Schepie/7segment/Images/7segment_exploded.png

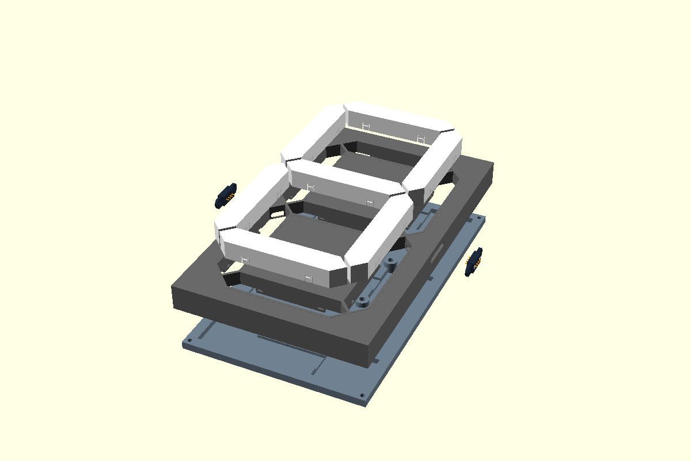
Images/7segment_exploded.png
