Schepie/7segment/Images/20261002_122156.jpg

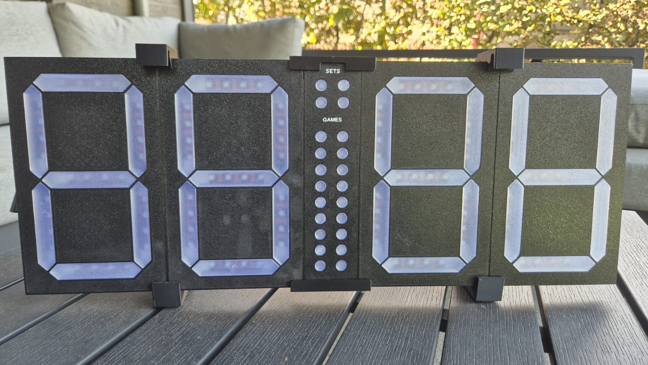
Images/20261002_122156.jpg
