Schepie/7segment/Images/20261002_122202.jpg

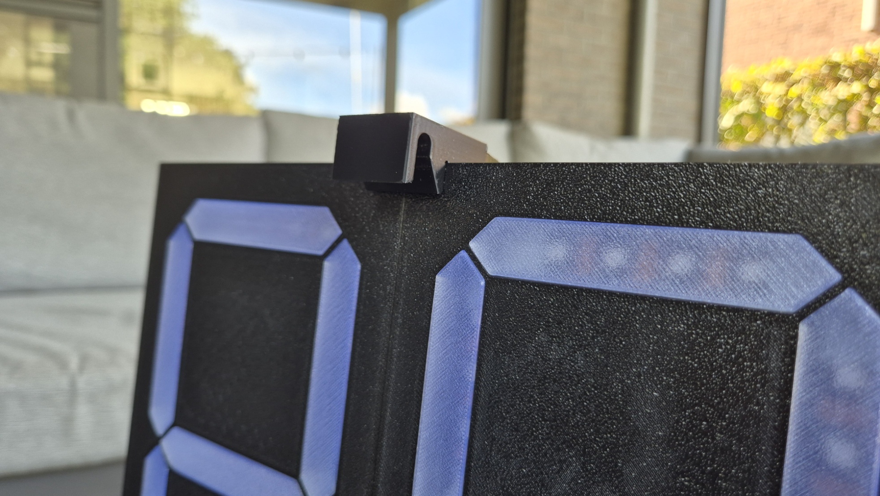
Images/20261002_122202.jpg
