Schepie/7segment/Images/20261002_122213.jpg

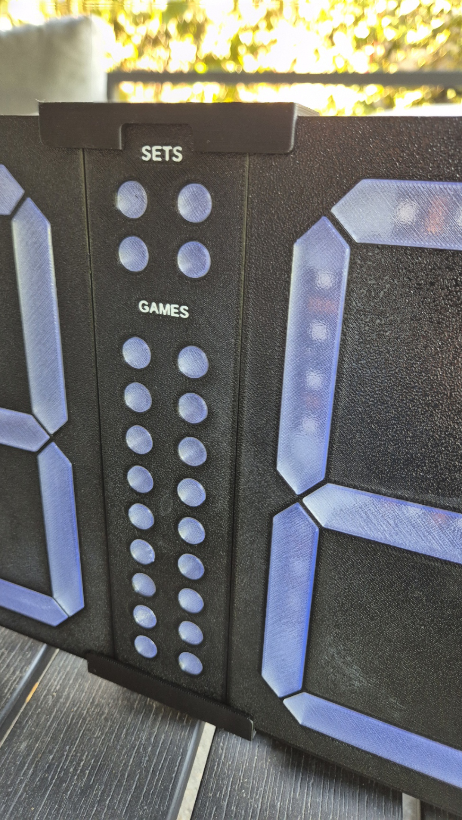
Images/20261002_122213.jpg
