Schepie/7segment/Images/20261002_122249.jpg

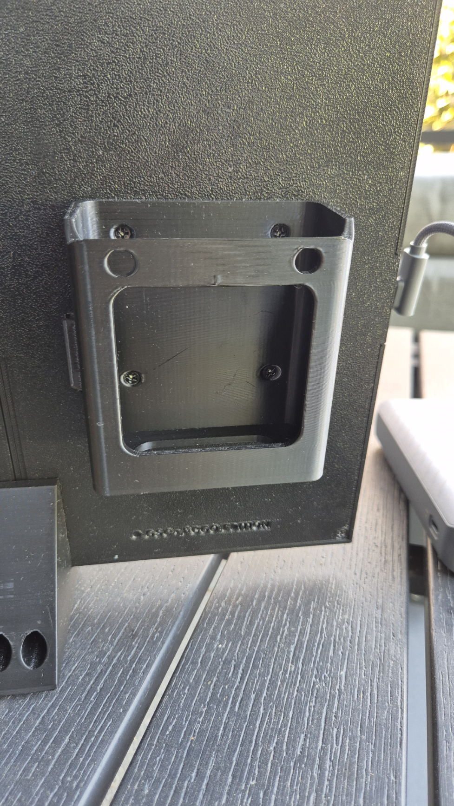
Images/20261002_122249.jpg
