Schepie/7segment/Images/20261002_122254.jpg

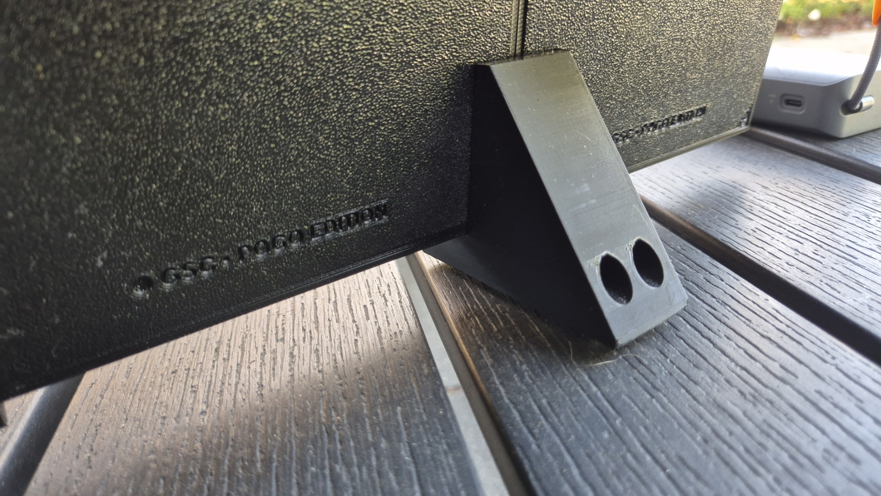
Images/20261002_122254.jpg
