Schepie/7segment/Images/20261002_122310.jpg

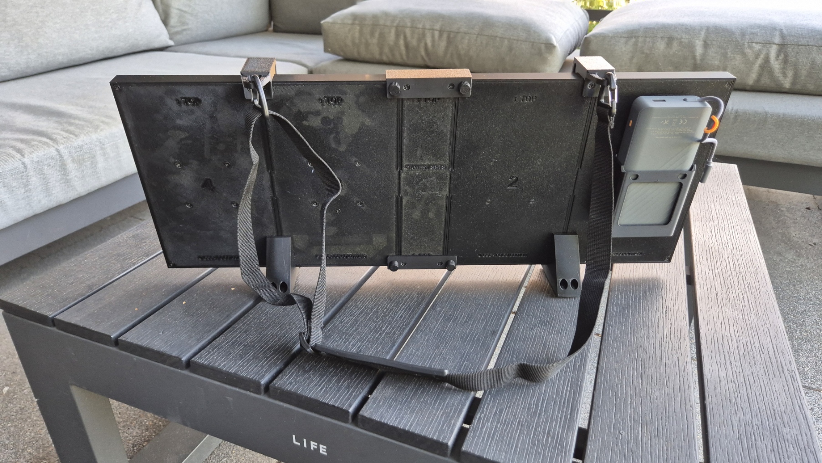
Images/20261002_122310.jpg
