Schepie/7segment/Images/20261002_122325.jpg

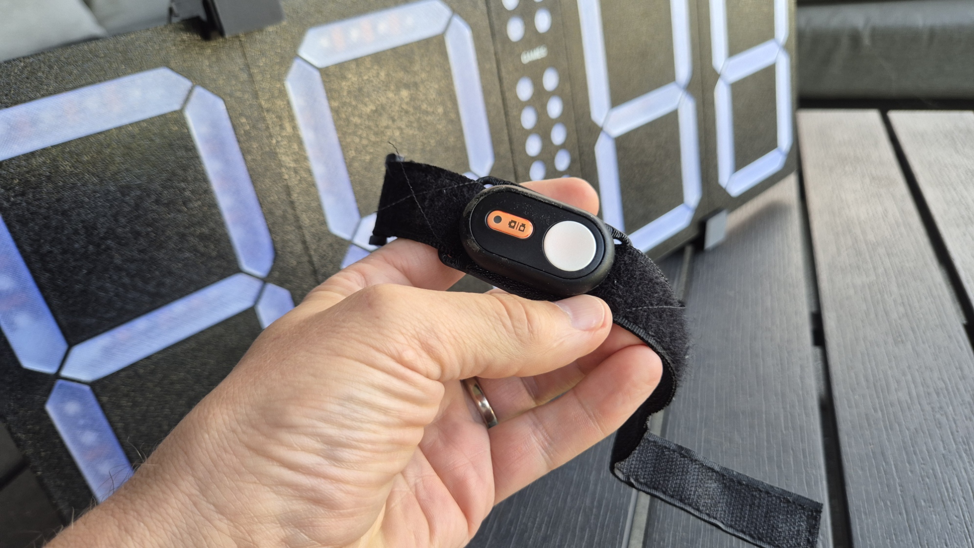
Images/20261002_122325.jpg
