Schepie/7segment/Images/20261002_122400.jpg

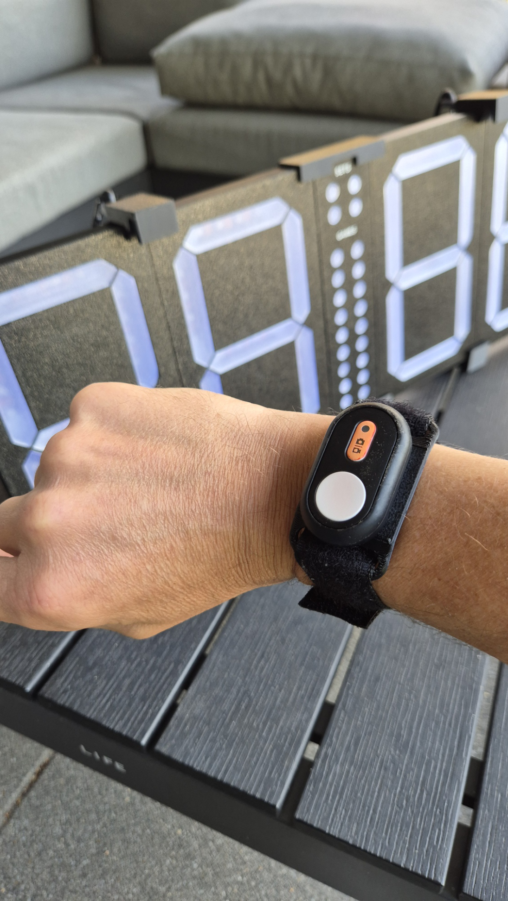
Images/20261002_122400.jpg
