Schepie/7segment/Images/20261002_122517.jpg

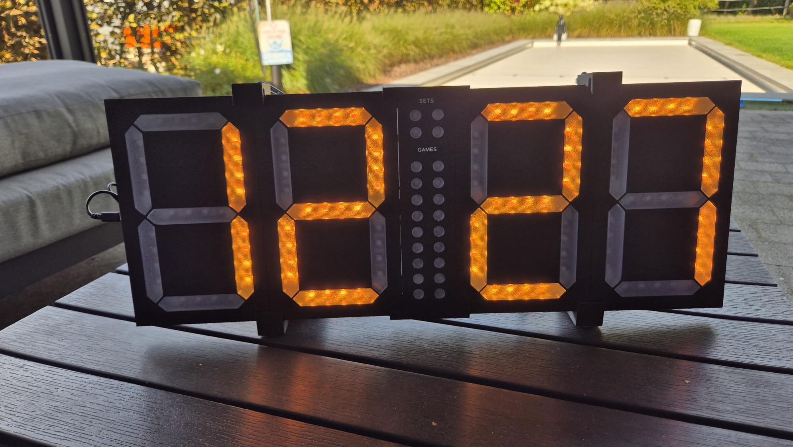
Images/20261002_122517.jpg
