Schepie/7segment/Images/20261002_122520.jpg

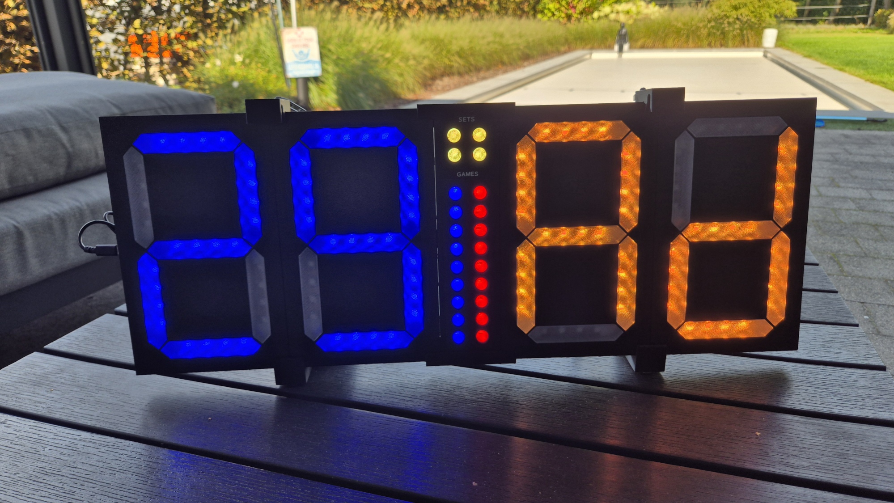
Images/20261002_122520.jpg
