Schepie/7segment/Images/20261002_122537.jpg

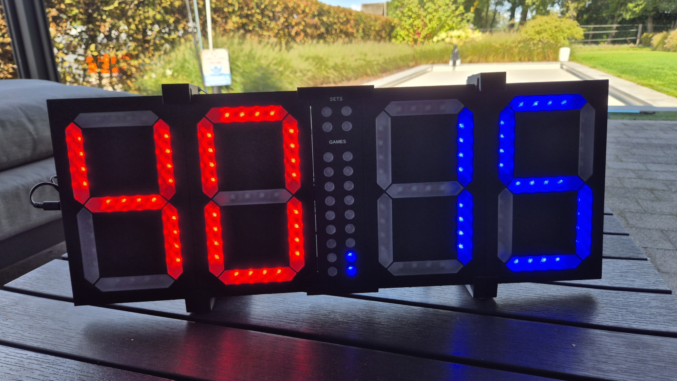
Images/20261002_122537.jpg
