Schepie/7segment/Images/20261002_122541.jpg

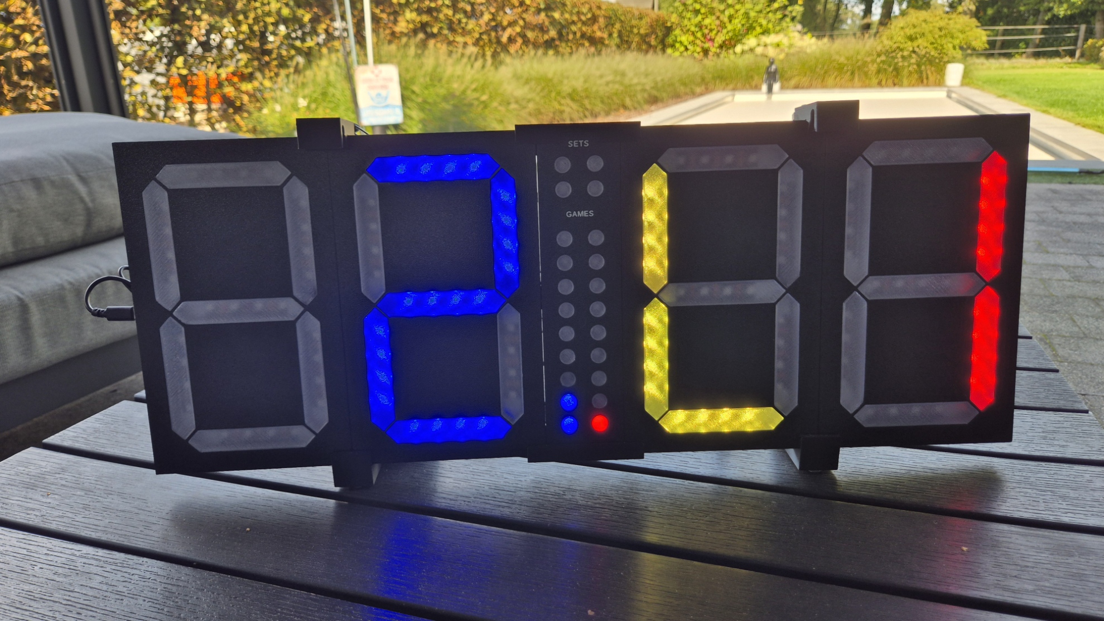
Images/20261002_122541.jpg
