Schepie/7segment/Images/20261002_122544.jpg

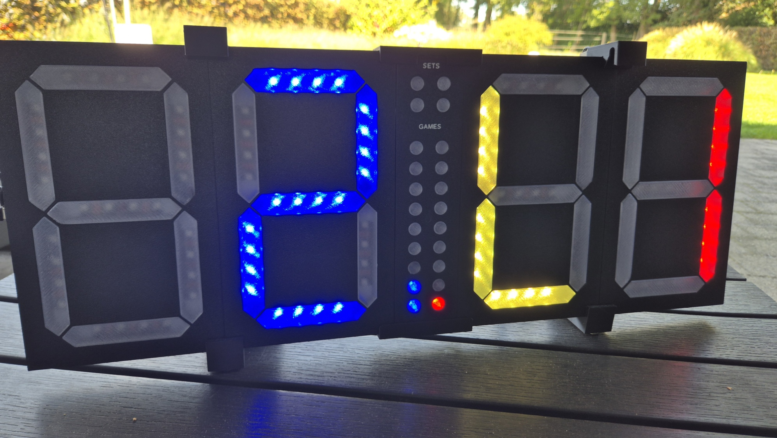
Images/20261002_122544.jpg
