Schepie/7segment/Images/20261002_122547.jpg

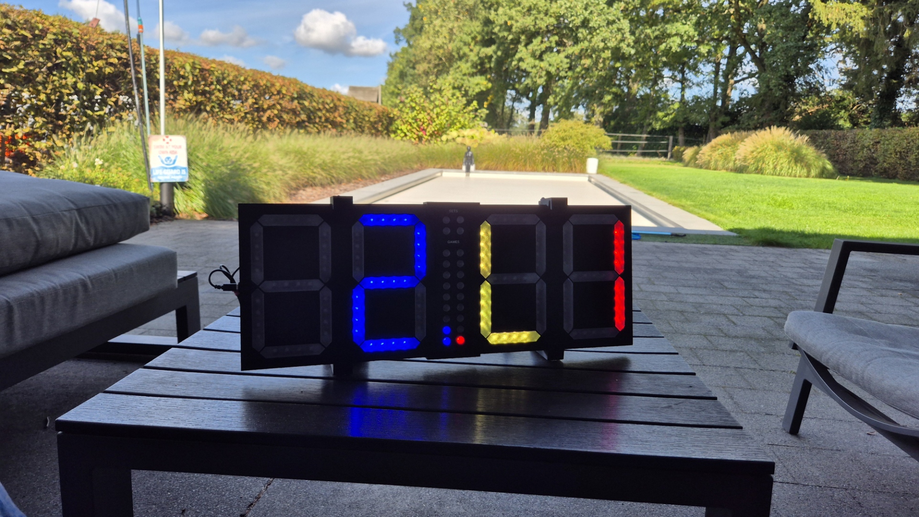
Images/20261002_122547.jpg
