Schepie/7segment/Images/20261002_122549.jpg

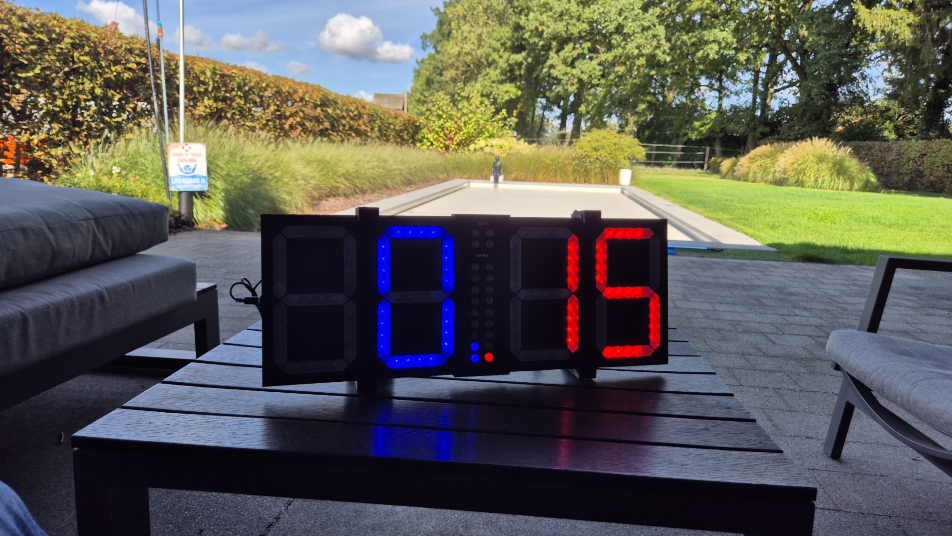
Images/20261002_122549.jpg
