Schepie/7segment/Images/20261002_123313.jpg

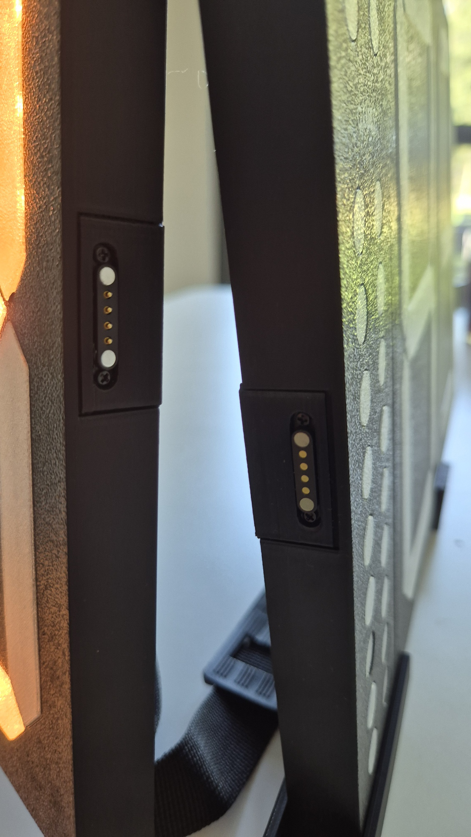
Images/20261002_123313.jpg
