Schepie/7segment/Images/20261002_123319.jpg

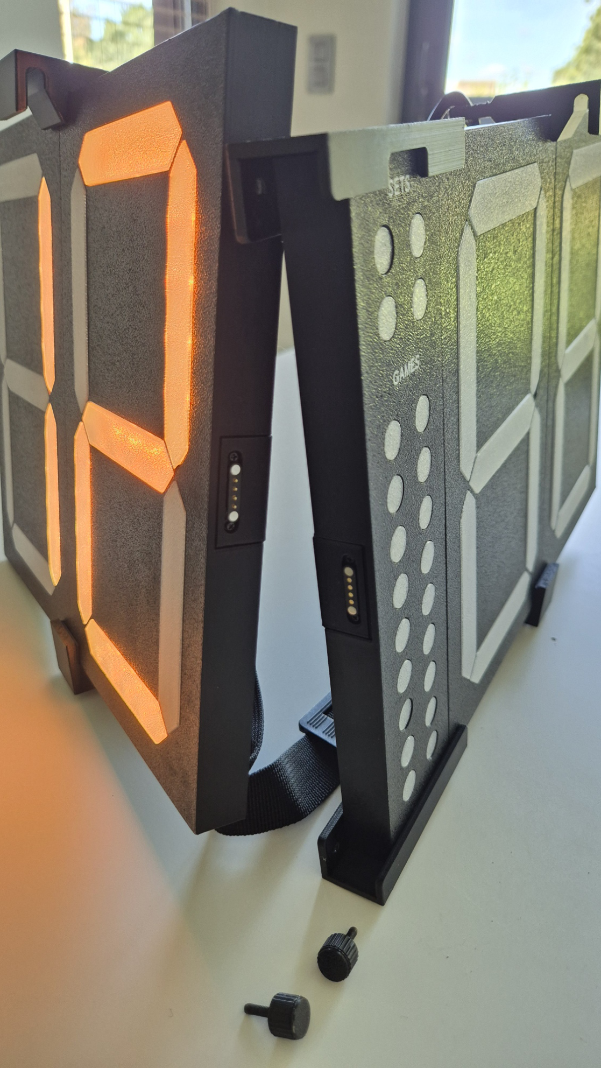
Images/20261002_123319.jpg
