Schepie/7segment/Images/board_back_2.jpeg

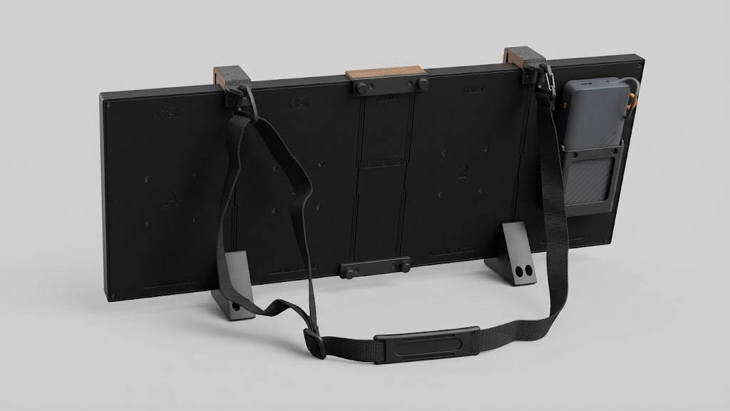
Images/board_back_2.jpeg
