Schepie/7segment/Images/bt_button_remote.png

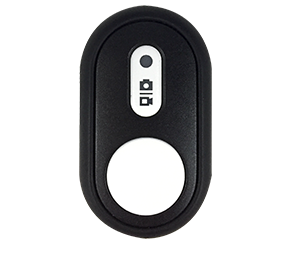
Images/bt_button_remote.png
