Schepie/7segment/Images/colon_check.png

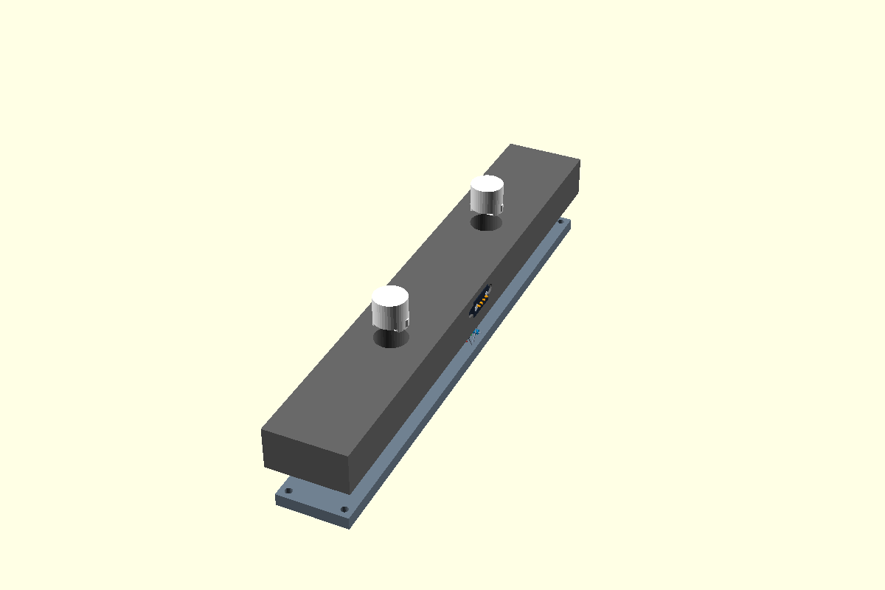
Images/colon_check.png
