Schepie/7segment/Images/crop_digit0.png

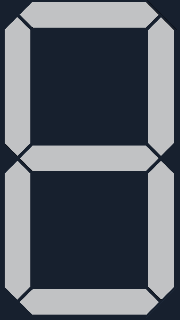
Images/crop_digit0.png
