Schepie/7segment/Images/display_stand_cradle_pair.png

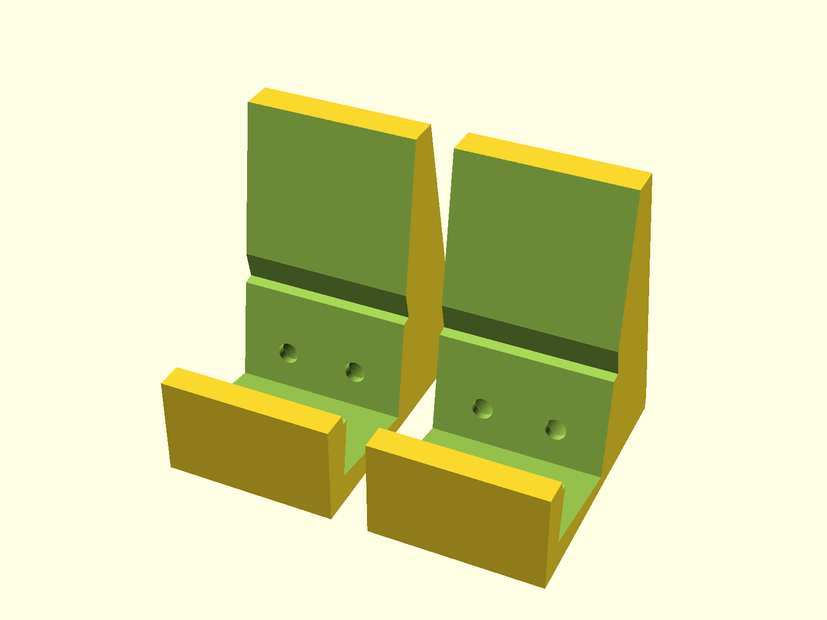
Images/display_stand_cradle_pair.png
