Schepie/7segment/Images/full_scoreboard_exploded.png

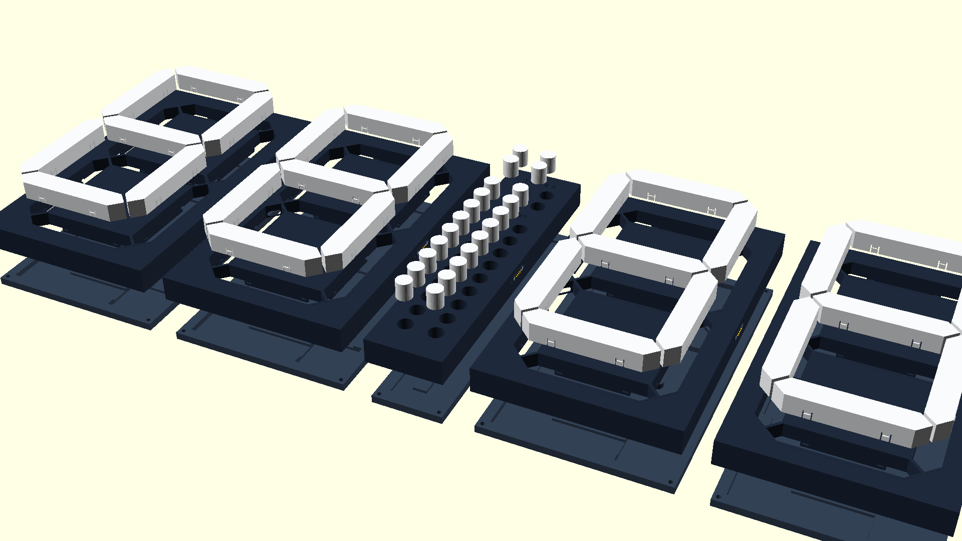
Images/full_scoreboard_exploded.png
