Schepie/7segment/Images/full_scoreboard_front.png

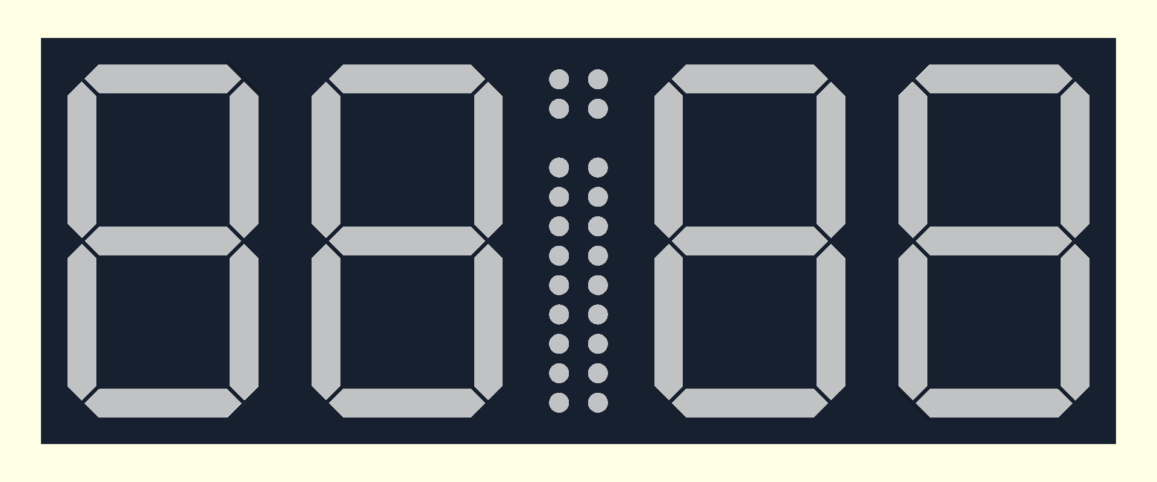
Images/full_scoreboard_front.png
