Schepie/7segment/Images/full_scoreboard_preview.png

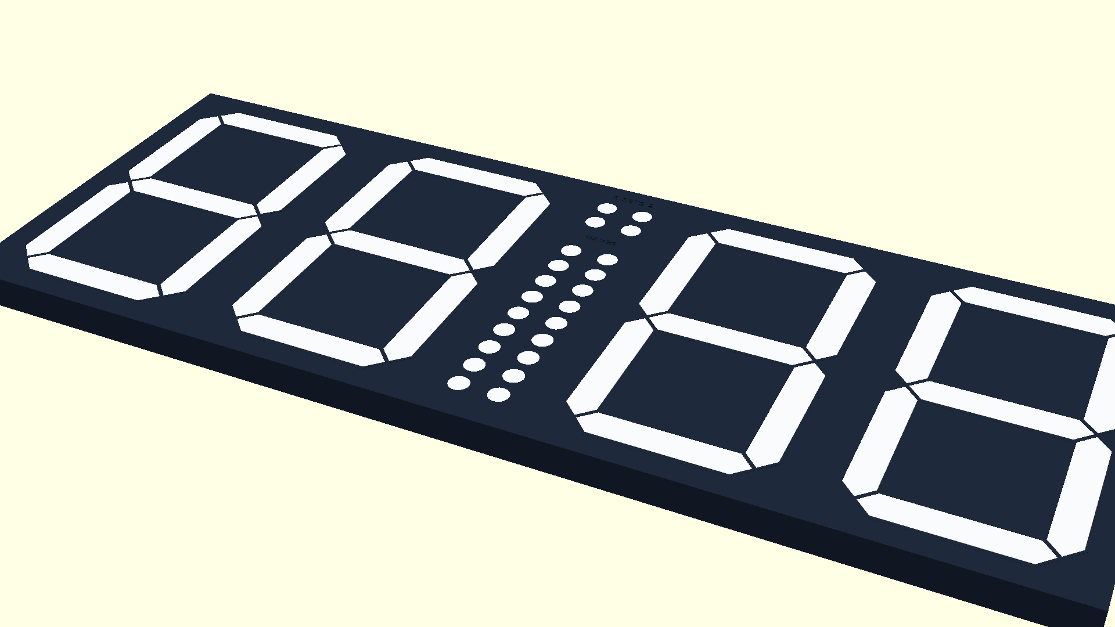
Images/full_scoreboard_preview.png
