Schepie/7segment/Images/full_scoreboard_rear.png

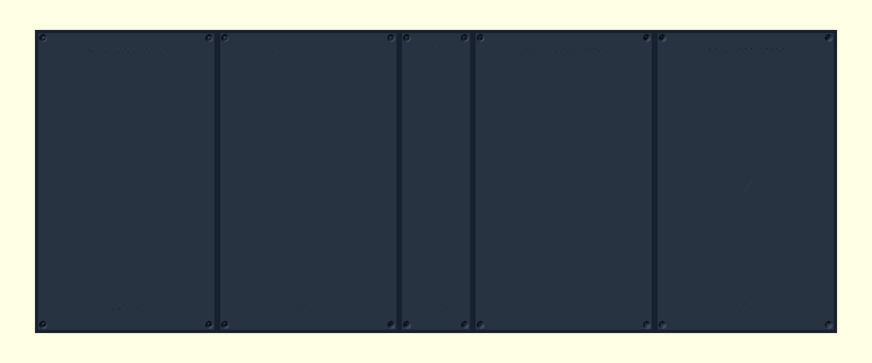
Images/full_scoreboard_rear.png
