Schepie/7segment/Images/padel_carrying_hanging_playing.webp

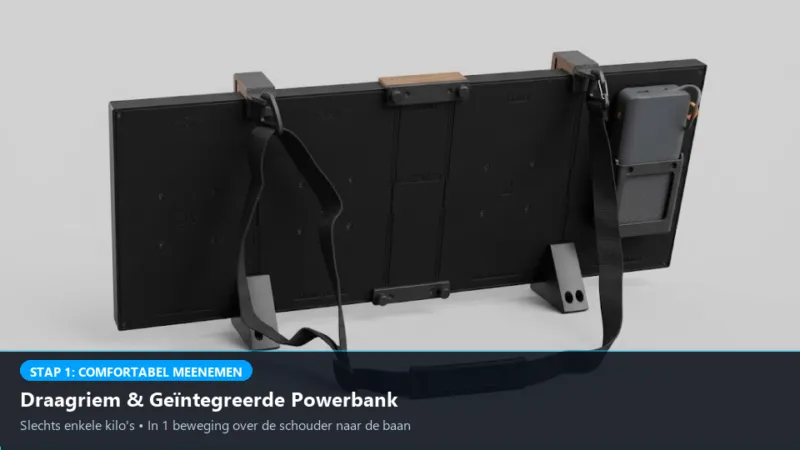
Images/padel_carrying_hanging_playing.webp
