Schepie/7segment/Images/padel_carrying_to_court.jpg

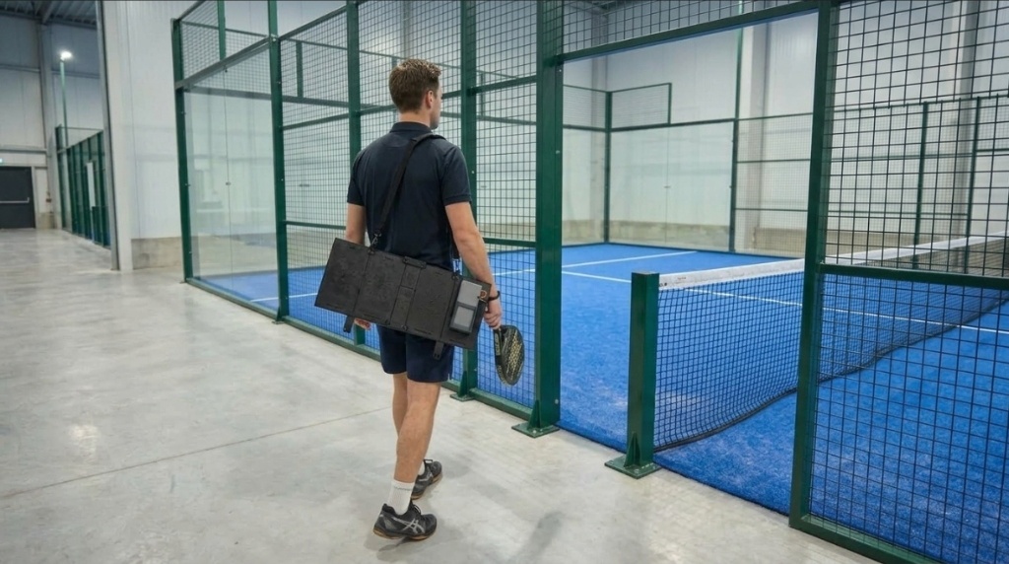
Images/padel_carrying_to_court.jpg
