Schepie/7segment/Images/padel_match_animatie.webp

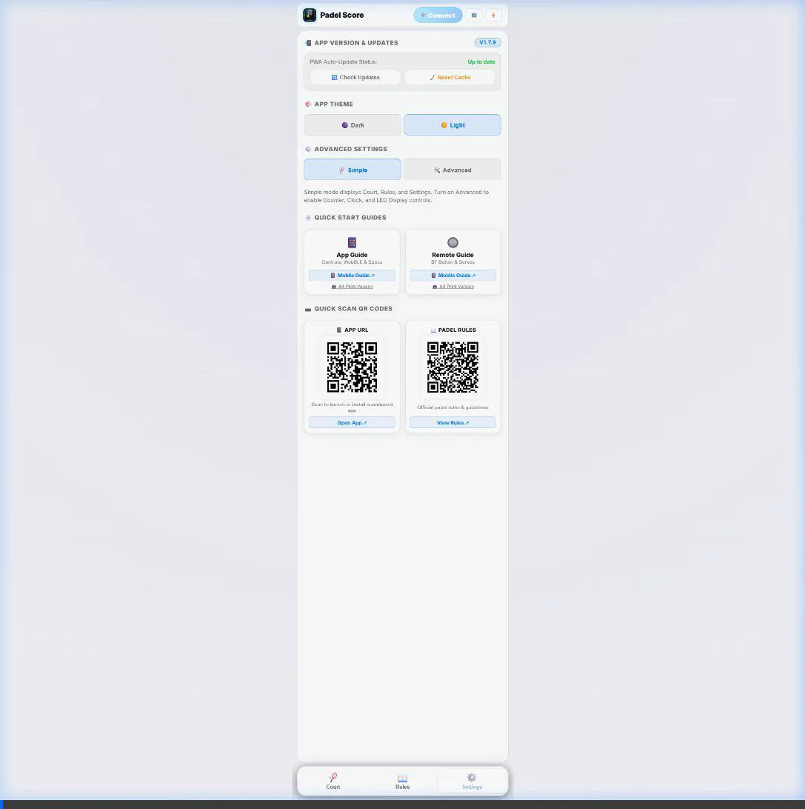
Images/padel_match_animatie.webp
