Schepie/7segment/Images/padel_panel_3dprinted_hooks.jpg

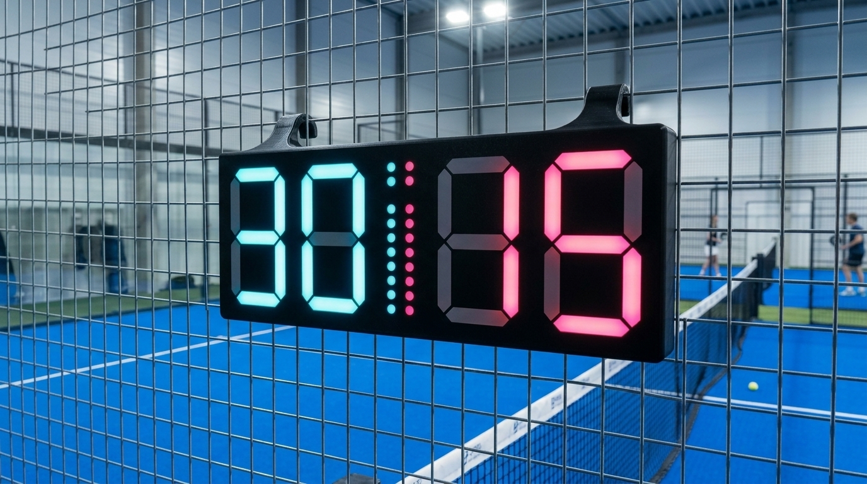
Images/padel_panel_3dprinted_hooks.jpg
