Schepie/7segment/Images/padel_panel_battery_holder.jpg

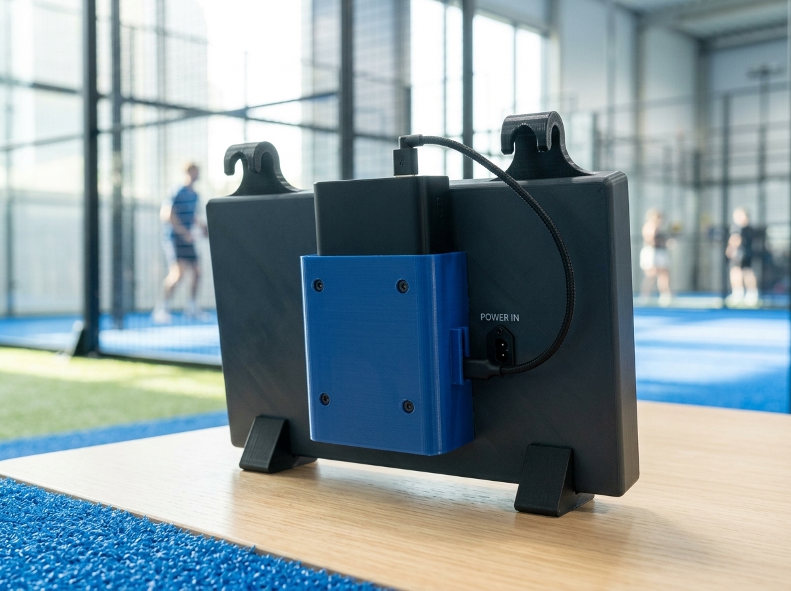
Images/padel_panel_battery_holder.jpg
