Schepie/7segment/Images/padel_panel_carried_strap.jpg

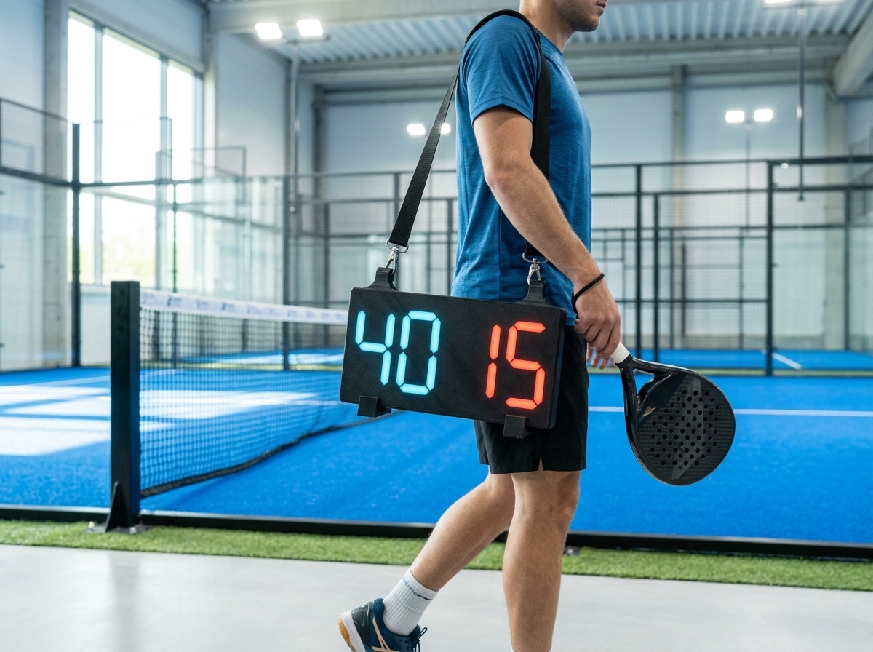
Images/padel_panel_carried_strap.jpg
