Schepie/7segment/Images/padel_panel_standing_court.jpg

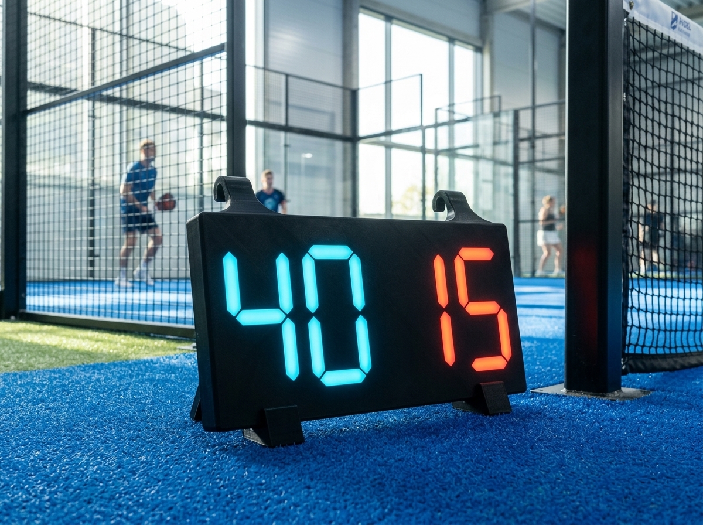
Images/padel_panel_standing_court.jpg
