Schepie/7segment/Images/padel_playing_match_action.jpg

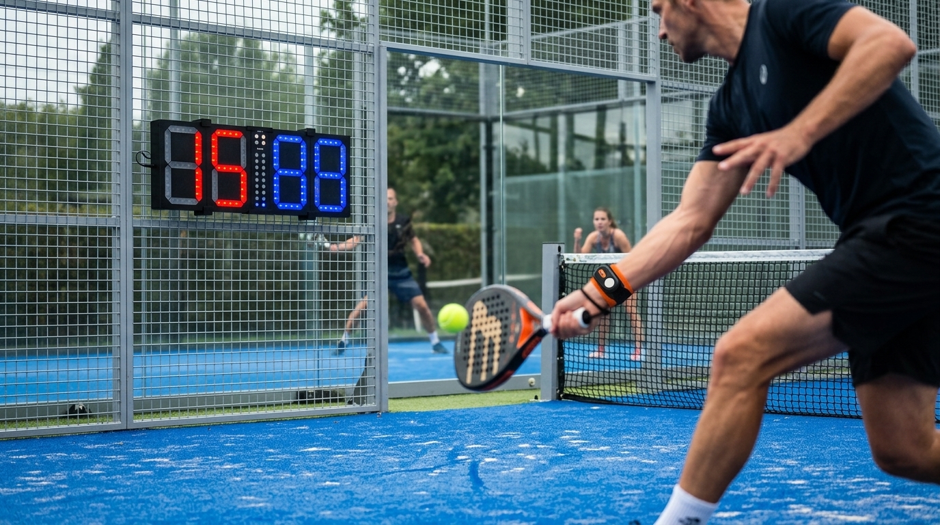
Images/padel_playing_match_action.jpg
