Schepie/7segment/Images/padel_remote_wrist_action.jpg

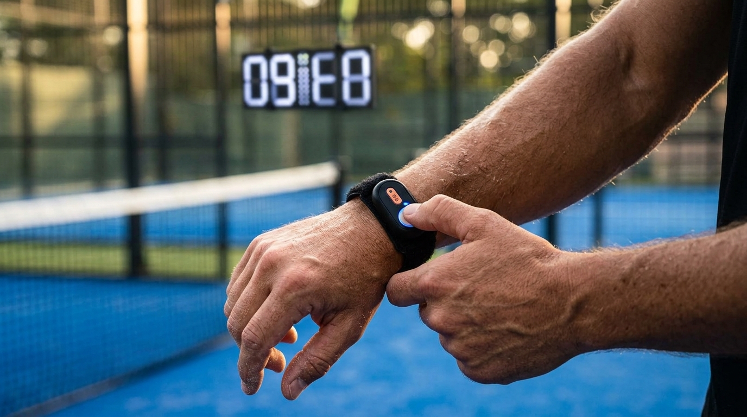
Images/padel_remote_wrist_action.jpg
