Schepie/7segment/qr_app.png

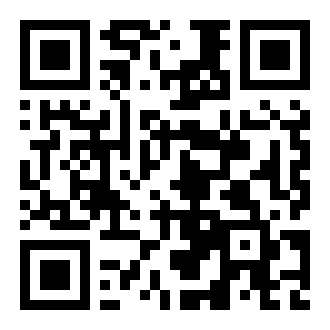
qr_app.png
