Schepie/7segment/qr_rules.png

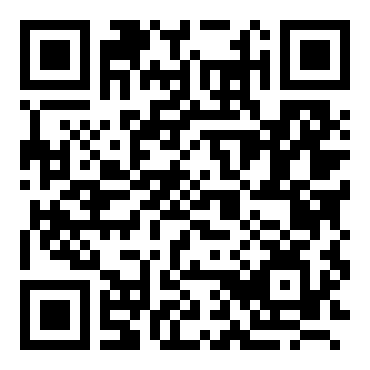
qr_rules.png
