Schepie/7segment/qr_voordelen.png

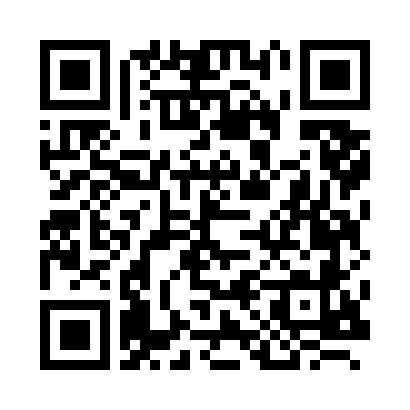
qr_voordelen.png
