Schepie/7segment/scad/display_stand_cradle_bottom_view.png

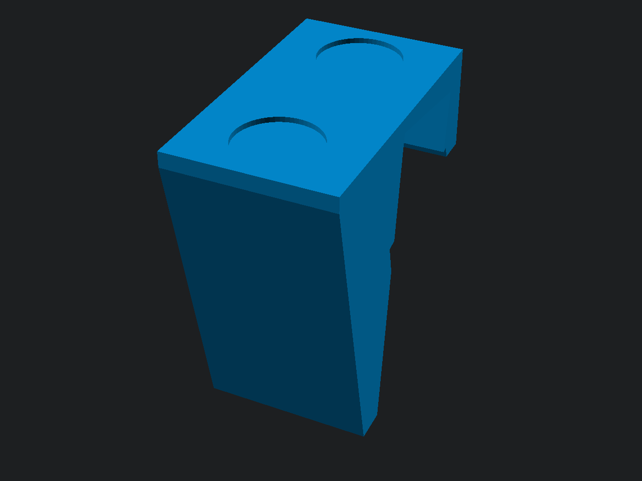
scad/display_stand_cradle_bottom_view.png
