Schepie/7segment/scad/display_stand_rear_view.png

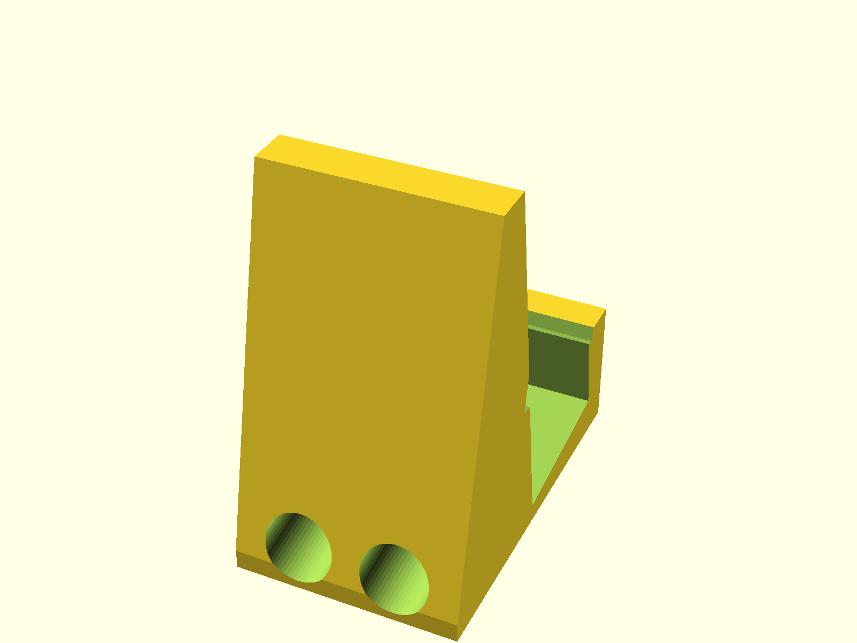
scad/display_stand_rear_view.png
