Schepie/7segment/scad/display_stand_screw_mount_pair.png

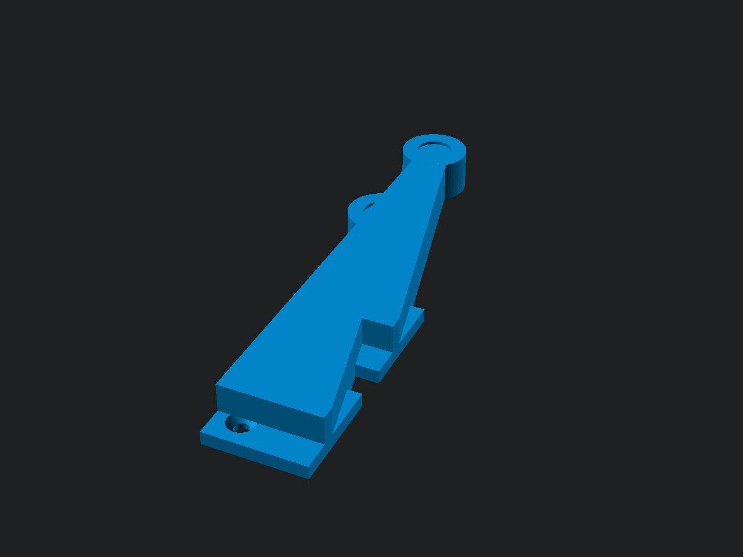
scad/display_stand_screw_mount_pair.png
