Schepie/7segment/scad/display_stand_seam_rear.png

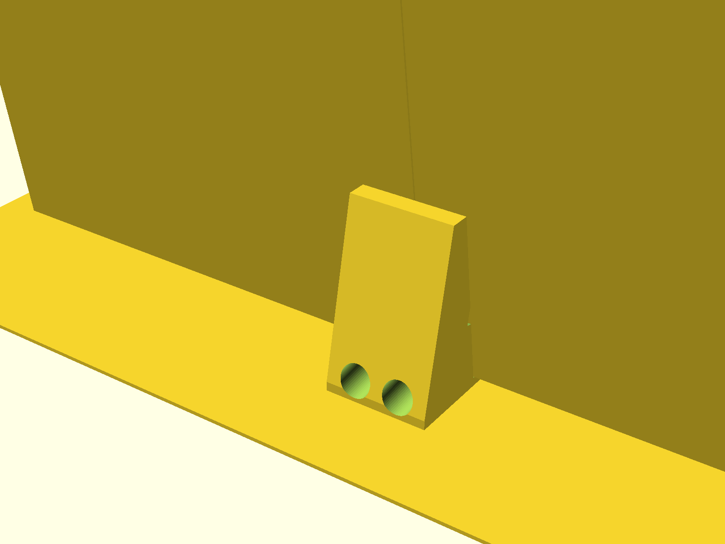
scad/display_stand_seam_rear.png
