Schepie/7segment/scad/games_sets_sets_overlap_after.png

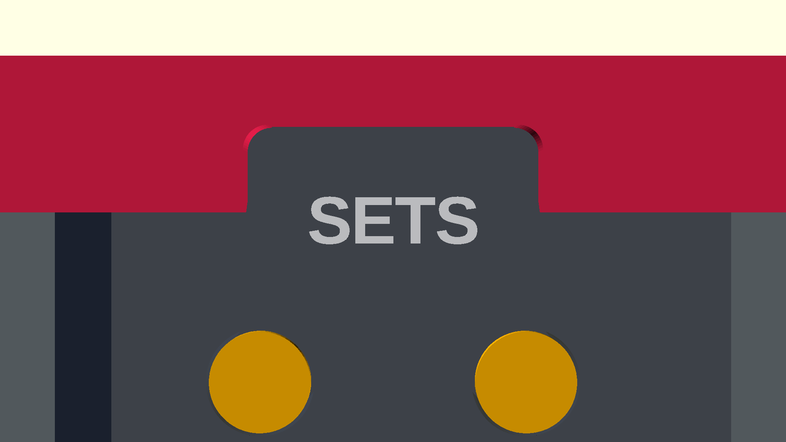
scad/games_sets_sets_overlap_after.png
