Schepie/7segment/scad/games_sets_u_bracket_corner_check.png

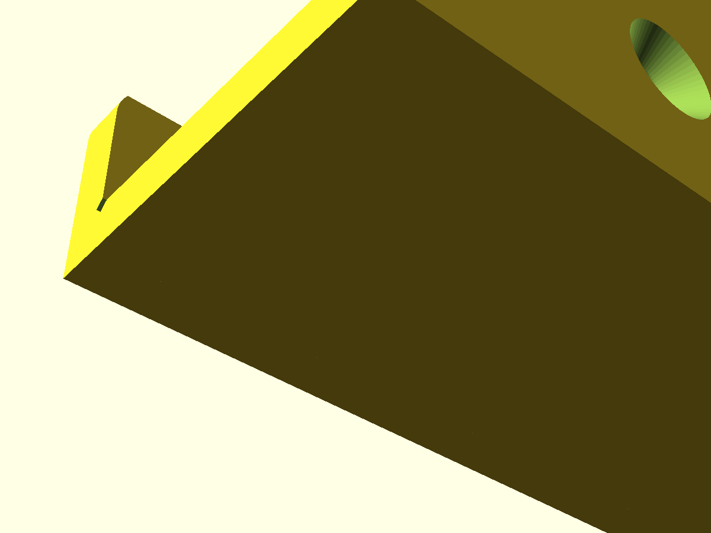
scad/games_sets_u_bracket_corner_check.png
