Schepie/7segment/scad/games_sets_u_bracket_cutaway.png

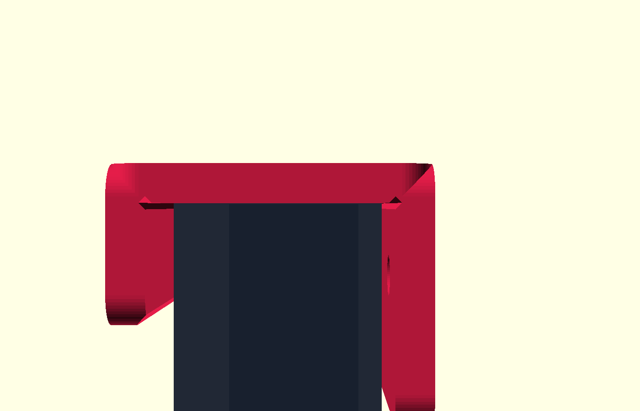
scad/games_sets_u_bracket_cutaway.png
