Schepie/7segment/scad/games_sets_u_bracket_front_view.png

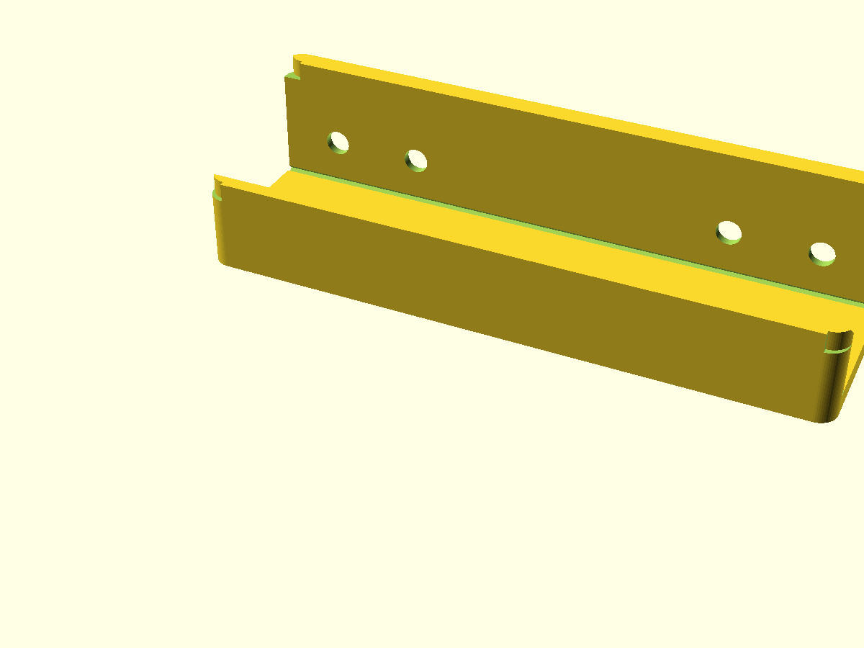
scad/games_sets_u_bracket_front_view.png
