Schepie/7segment/scad/games_sets_u_bracket_preview.png

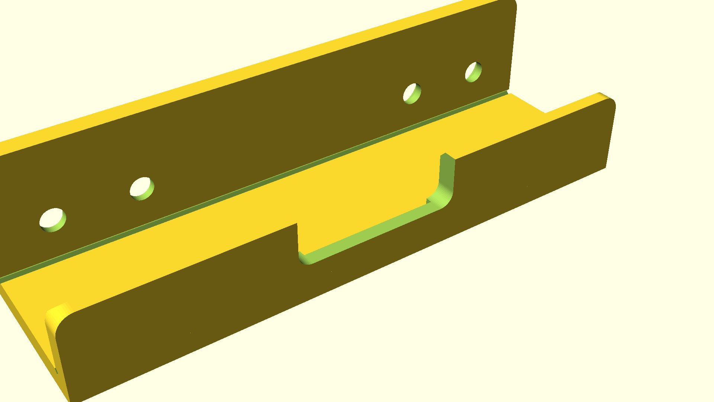
scad/games_sets_u_bracket_preview.png
