Schepie/7segment/scad/padel_battery_holder_vesa_front.png

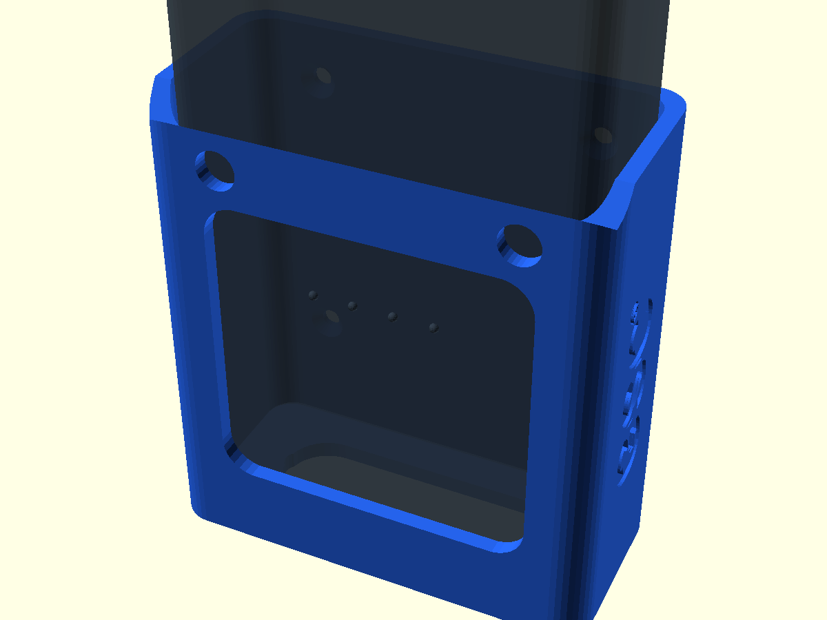
scad/padel_battery_holder_vesa_front.png
