Schepie/7segment/scad/padel_battery_holder_vesa_rear.png

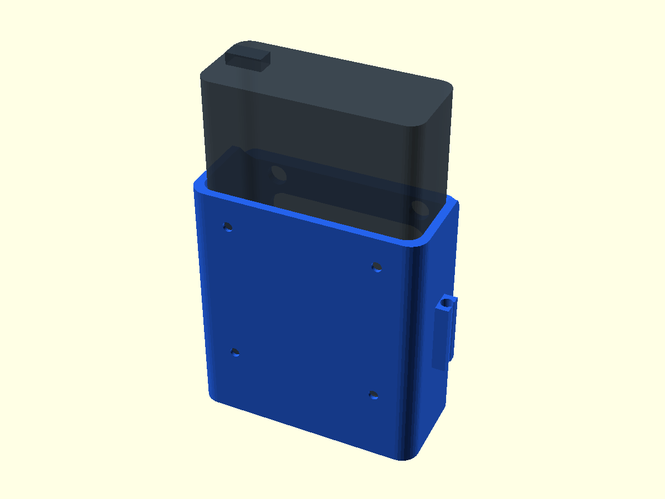
scad/padel_battery_holder_vesa_rear.png
