Schepie/7segment/scad/padel_mesh_hook_seam_single.png

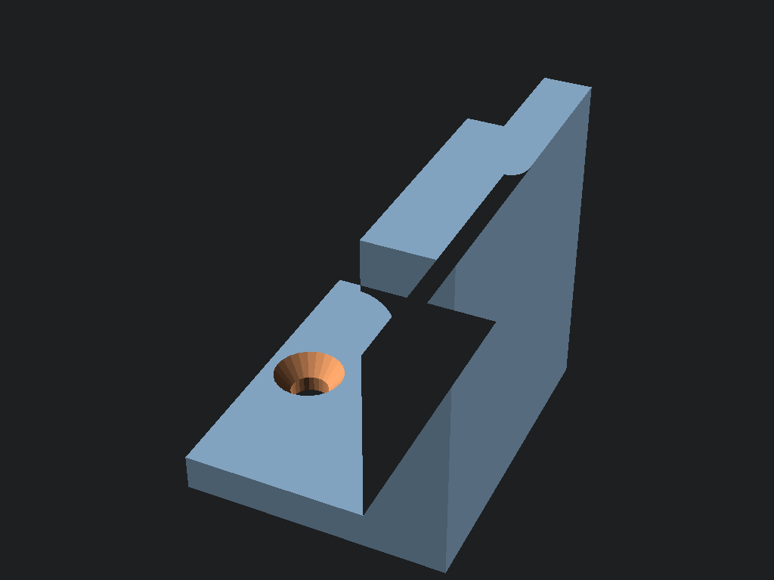
scad/padel_mesh_hook_seam_single.png
