Schepie/7segment/scad/panel3_wpt_interior_view.png

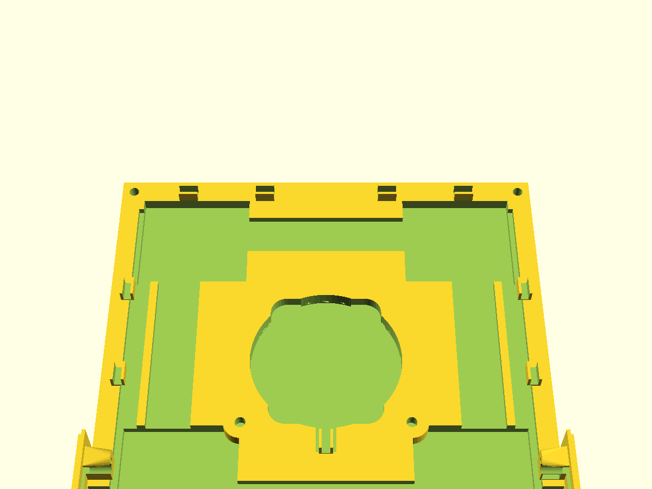
scad/panel3_wpt_interior_view.png
