Schepie/7segment/scad/panel3_wpt_rear_view.png

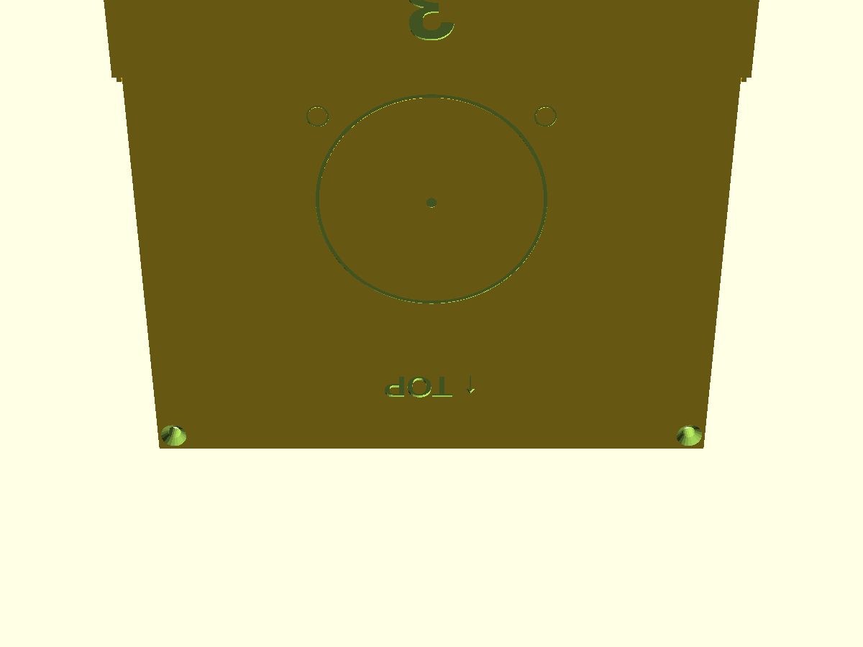
scad/panel3_wpt_rear_view.png
