Schepie/7segment/scad/panel_seam_u_bracket_preview.png

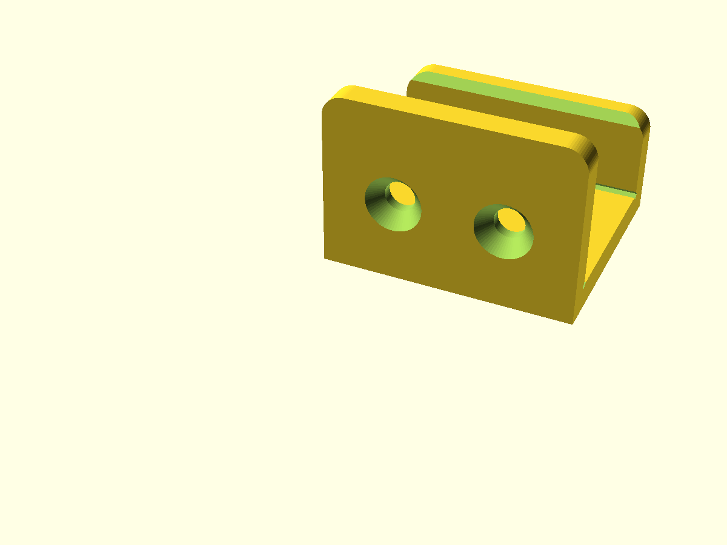
scad/panel_seam_u_bracket_preview.png
