Schepie/7segment/scad/panel_seam_u_bracket_set4_hook.png

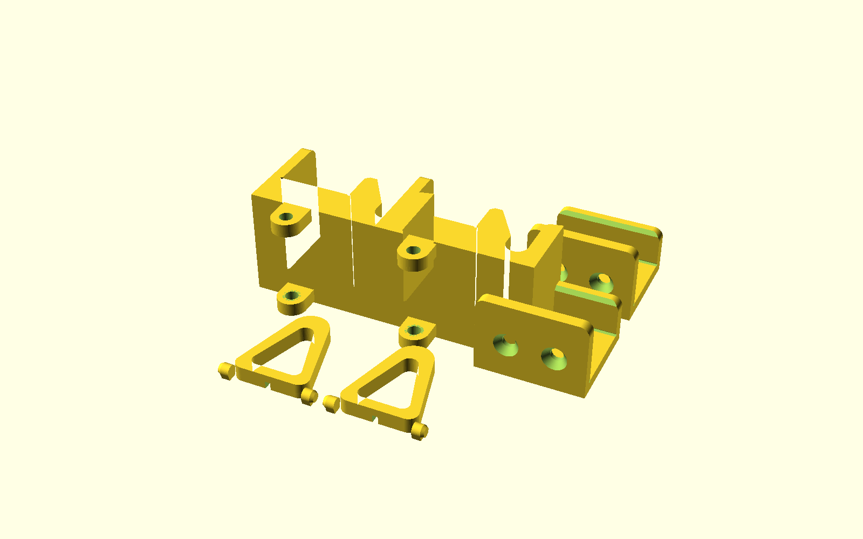
scad/panel_seam_u_bracket_set4_hook.png
