Schepie/7segment/scad/panel_seam_u_hook_bracket_rear_eye.png

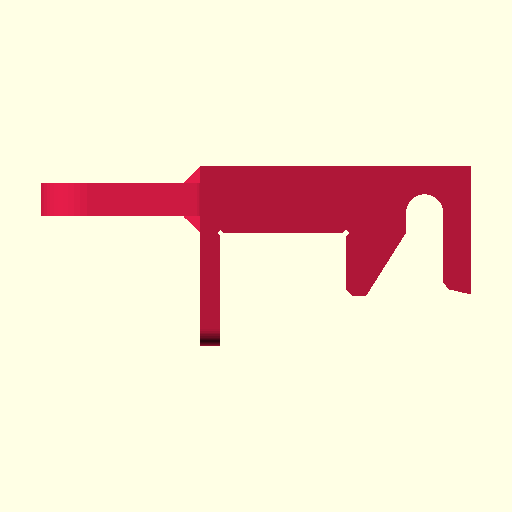
scad/panel_seam_u_hook_bracket_rear_eye.png
