Schepie/7segment/scad/panel_thumbscrew_cutaway.png

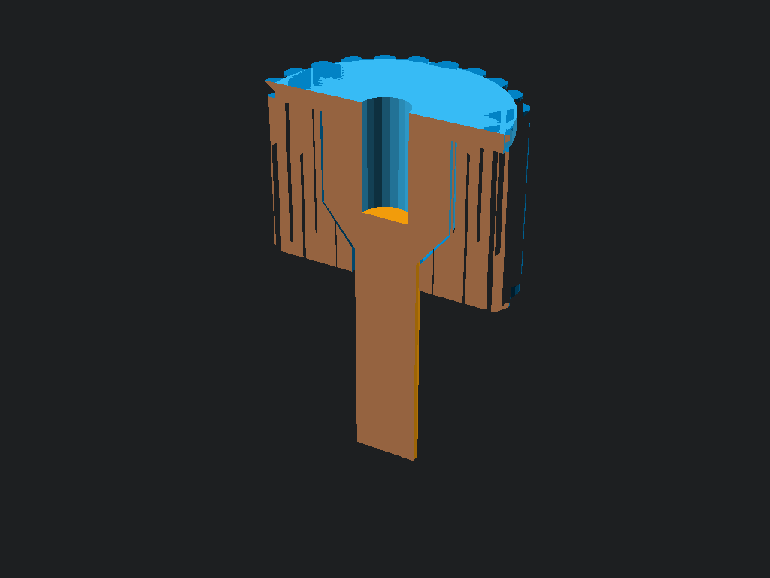
scad/panel_thumbscrew_cutaway.png
