Schepie/7segment/scad/panel_thumbscrew_insert_stud.png

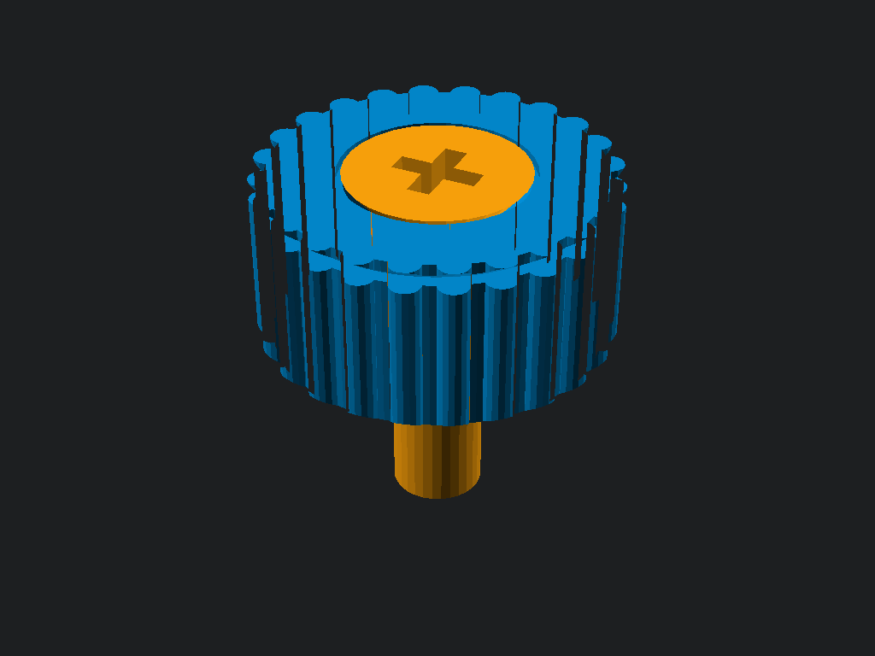
scad/panel_thumbscrew_insert_stud.png
