Schepie/7segment/scad/panel_thumbscrew_insert_stud_cutaway.png

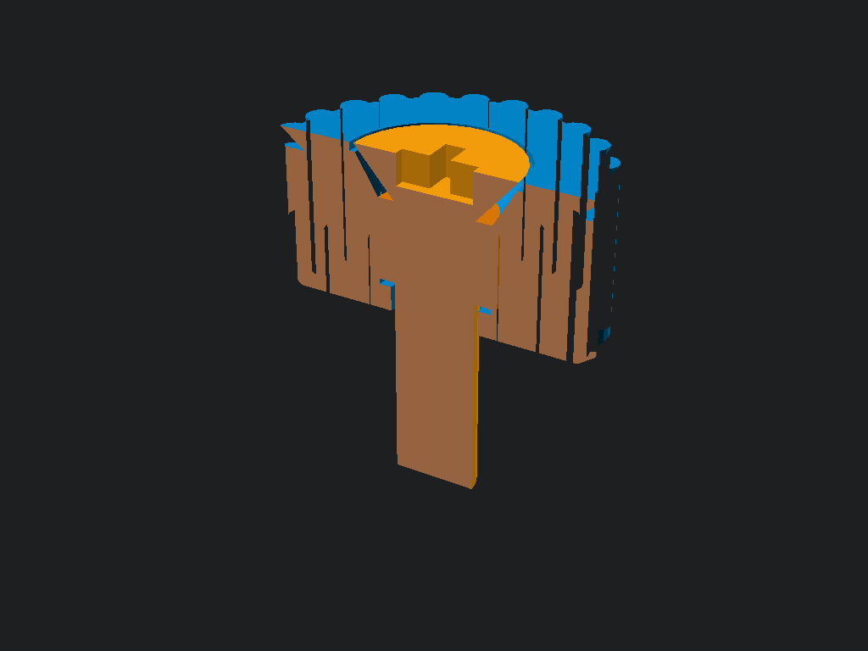
scad/panel_thumbscrew_insert_stud_cutaway.png
