Schepie/7segment/scad/panel_thumbscrew_pair.png

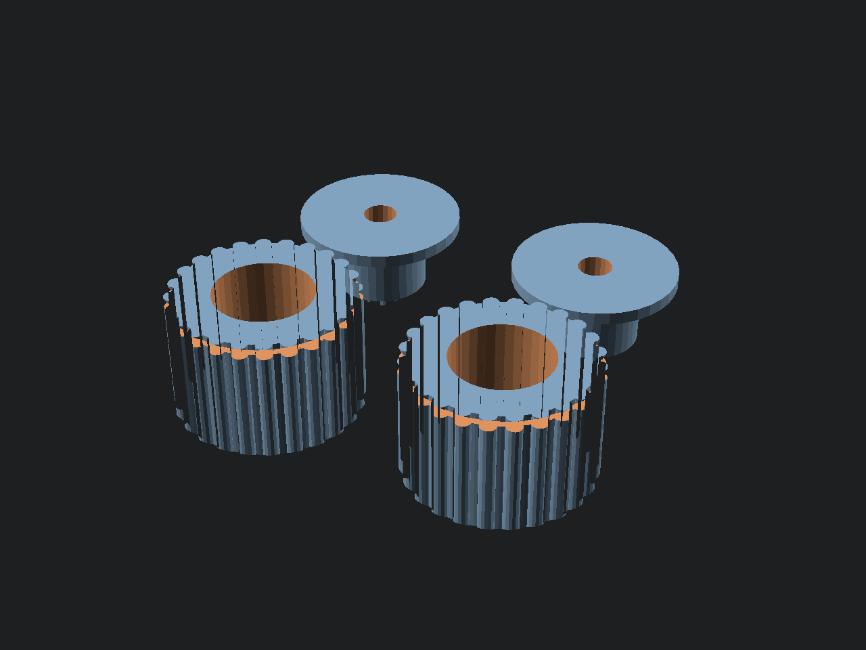
scad/panel_thumbscrew_pair.png
