Schepie/7segment/scad/panel_thumbscrew_thumb_nut.png

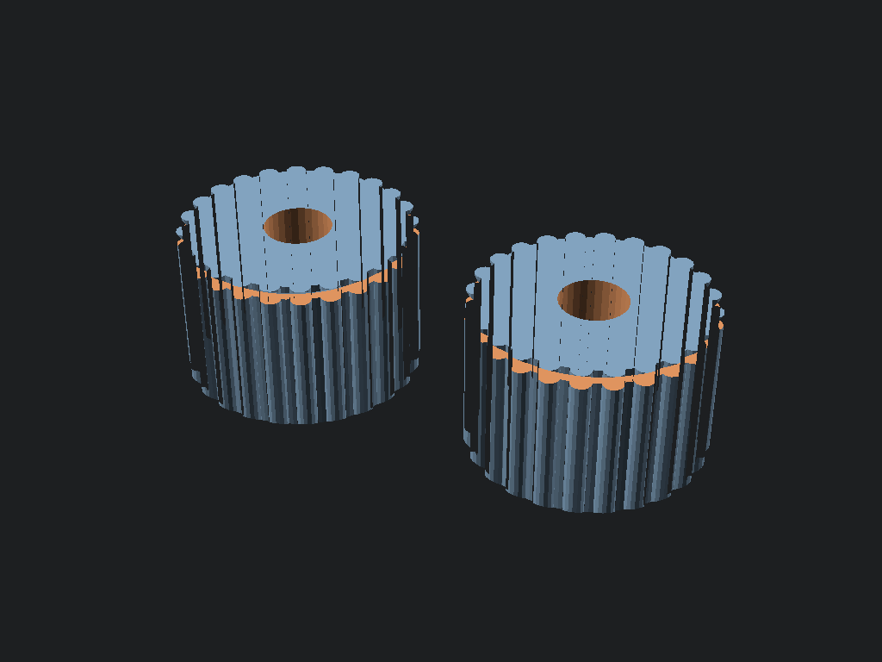
scad/panel_thumbscrew_thumb_nut.png
