Schepie/7segment/scad/rear_corner_foot.png

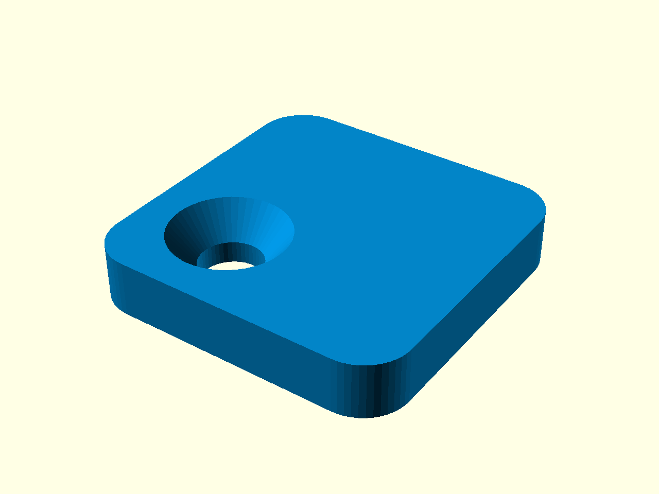
scad/rear_corner_foot.png
