Schepie/7segment/scad/rear_corner_foot_set4.png

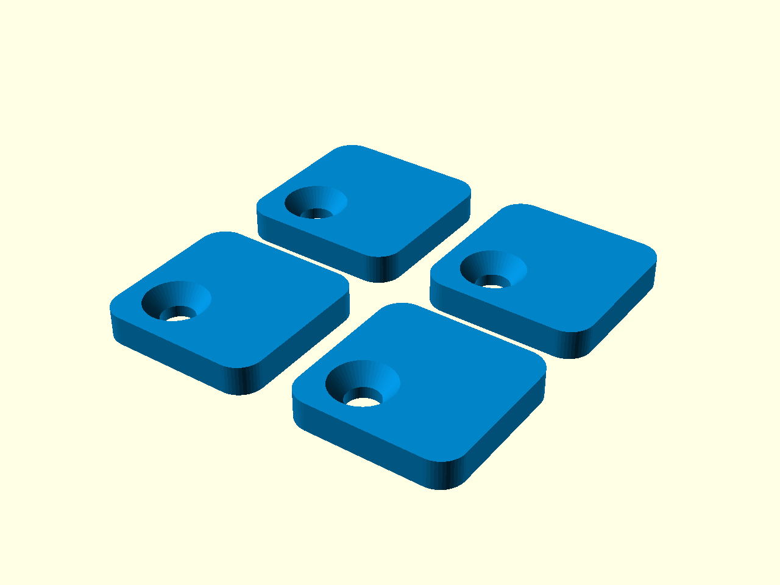
scad/rear_corner_foot_set4.png
