Schepie/7segment/scad/rear_joining_bracket_hinged_45deg.png

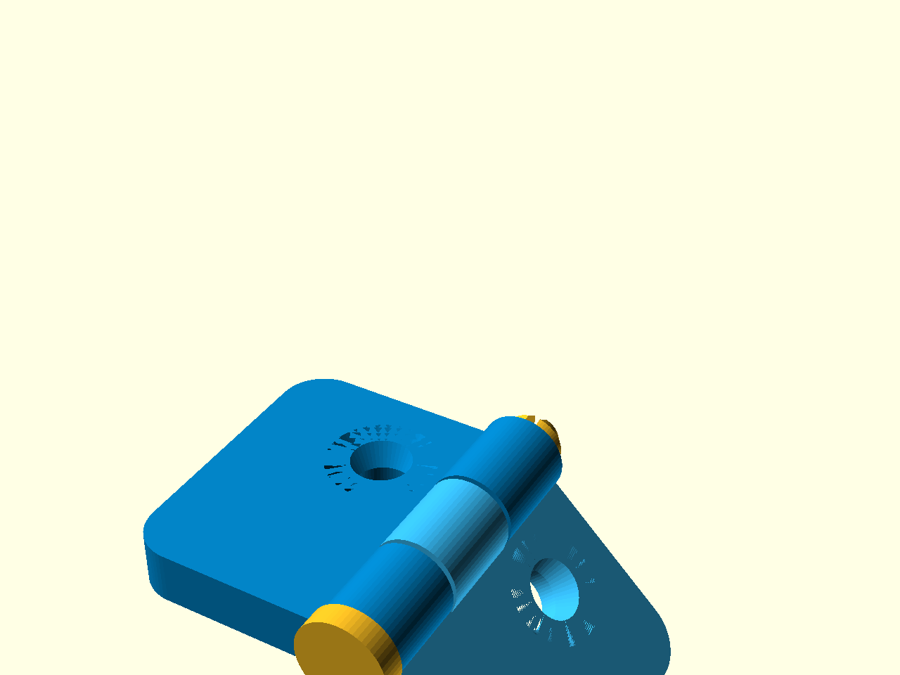
scad/rear_joining_bracket_hinged_45deg.png
