Schepie/7segment/scad/rear_joining_bracket_hinged_pair.png

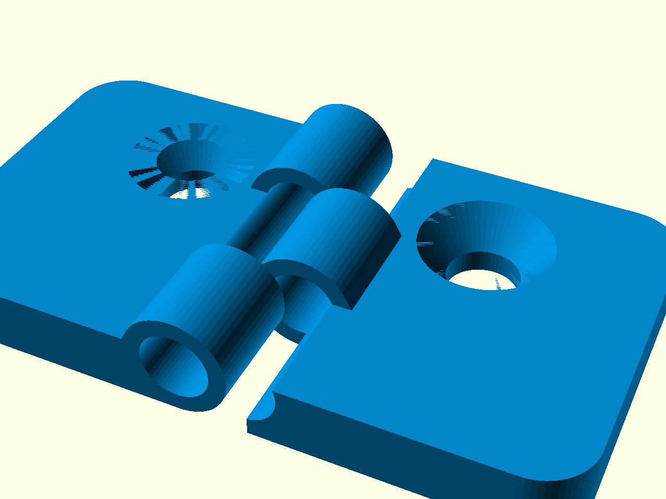
scad/rear_joining_bracket_hinged_pair.png
