Schepie/7segment/scad/rear_joining_bracket_hinged_set.png

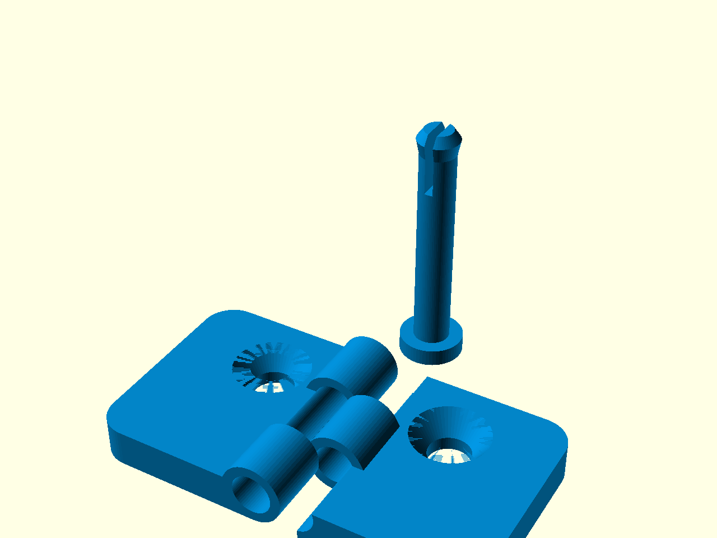
scad/rear_joining_bracket_hinged_set.png
