Schepie/7segment/scad/remote_strap_holder_both_preview.png

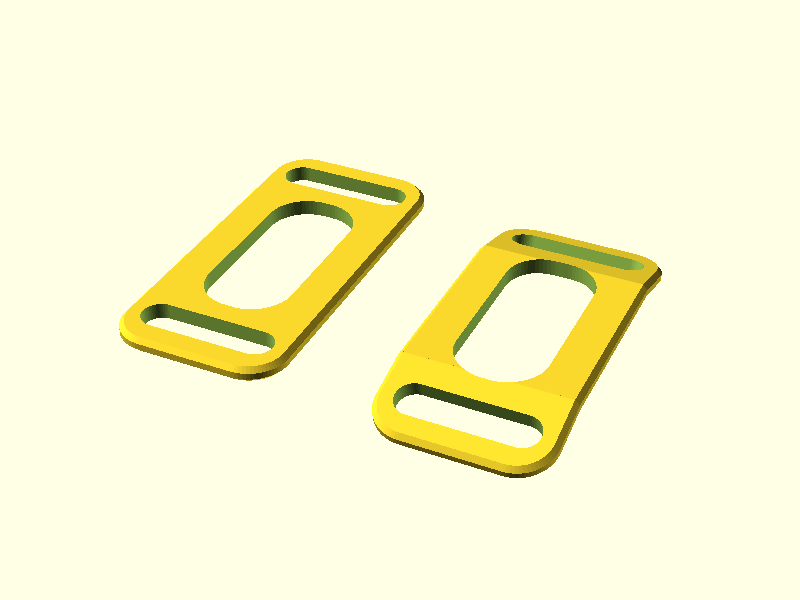
scad/remote_strap_holder_both_preview.png
