Schepie/7segment/scad/remote_strap_holder_preview.png

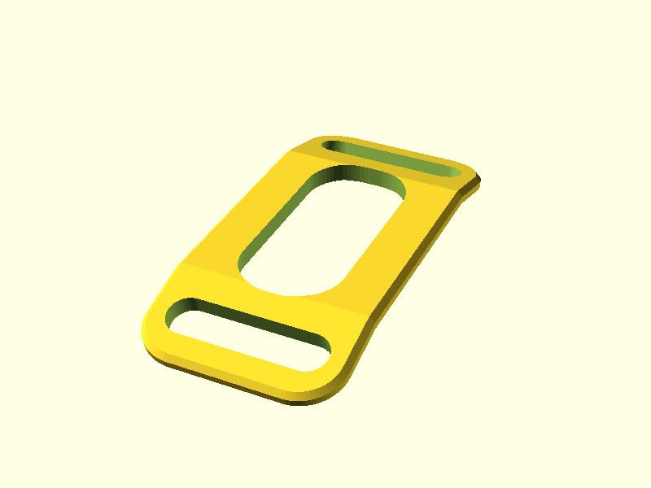
scad/remote_strap_holder_preview.png
