Schepie/7segment/scad/single_segment_white.png

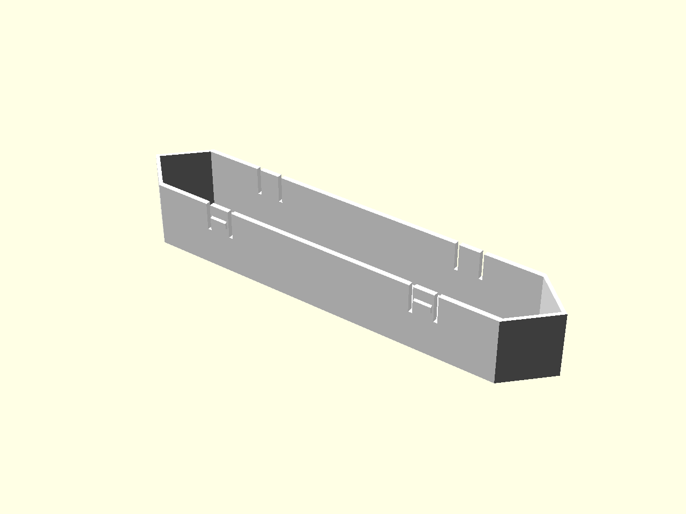
scad/single_segment_white.png
