Schepie/7segment/scad/single_segment_white_cutaway.png

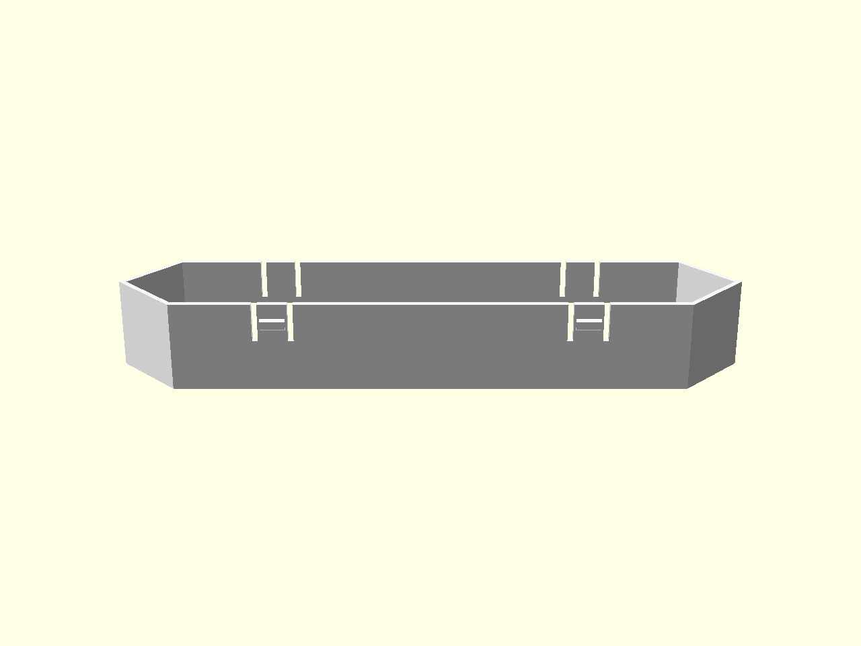
scad/single_segment_white_cutaway.png
