Schepie/7segment/scad/single_segment_white_digit_set.png

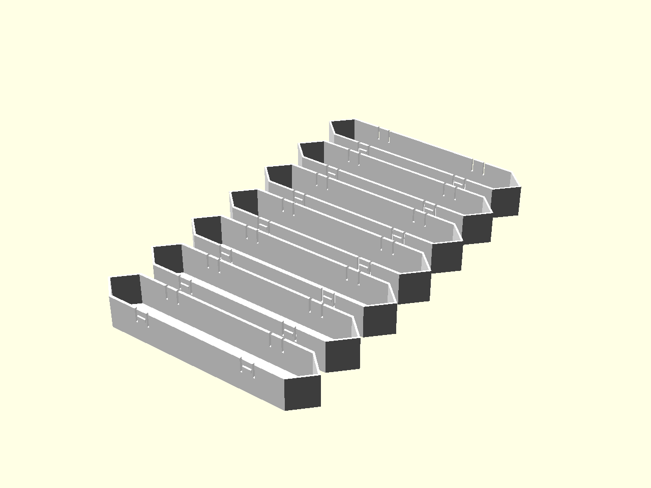
scad/single_segment_white_digit_set.png
