Schepie/7segment/scad/vesa_wpt_70x110_interior.png

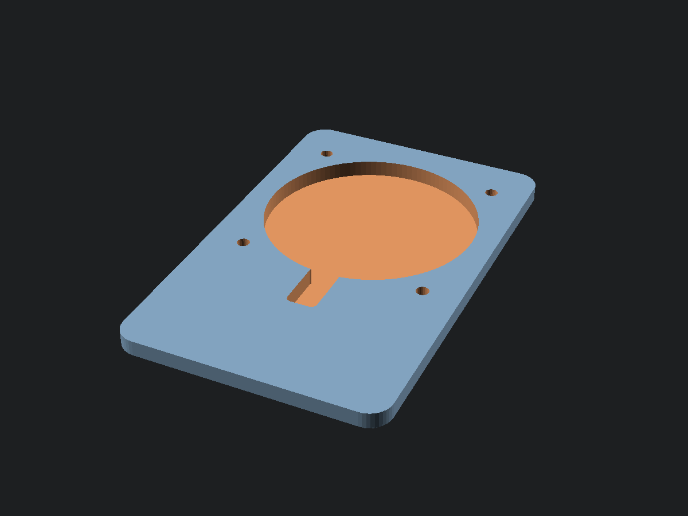
scad/vesa_wpt_70x110_interior.png
