Schepie/7segment/scad/vesa_wpt_70x110_rear.png

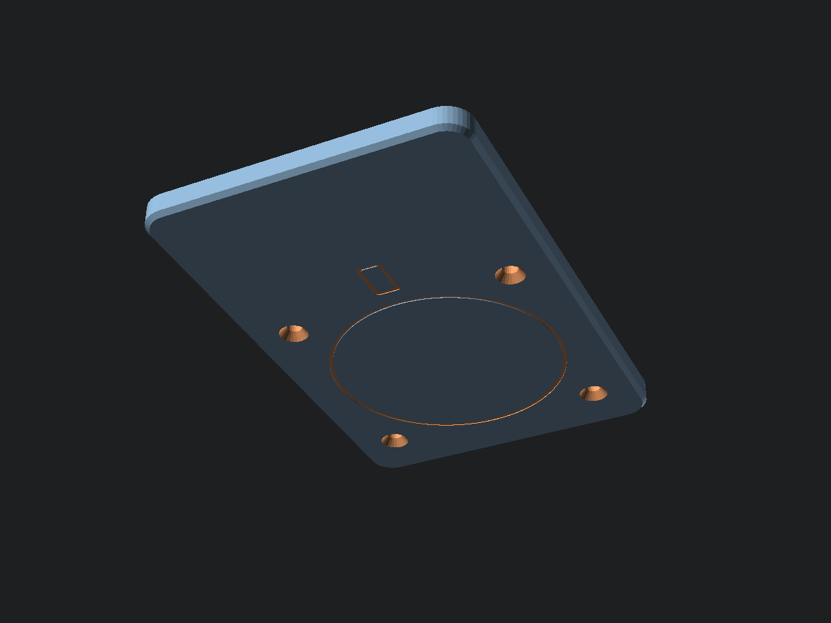
scad/vesa_wpt_70x110_rear.png
