Schepie/7segment/scad/vesa_wpt_cutaway.png

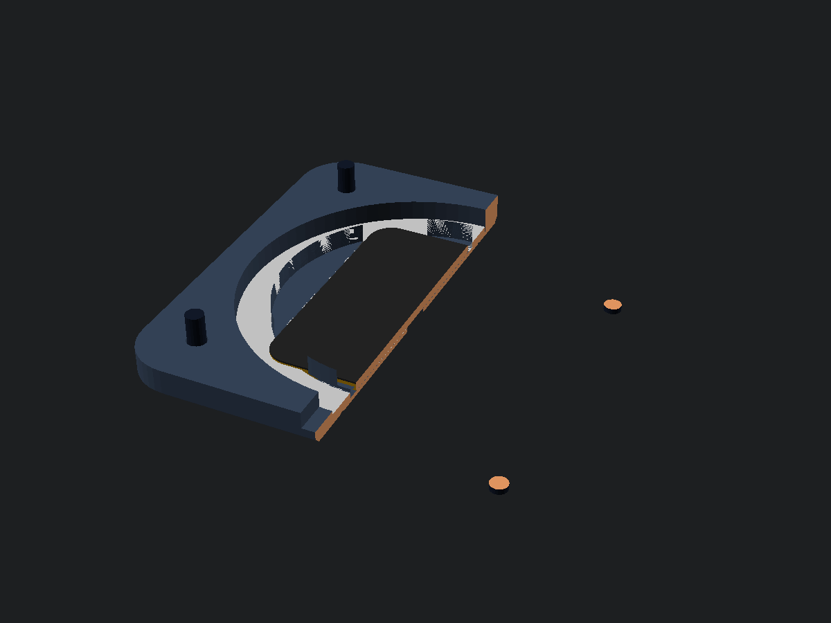
scad/vesa_wpt_cutaway.png
