Schepie/7segment/scad/vesa_wpt_multicolor.png

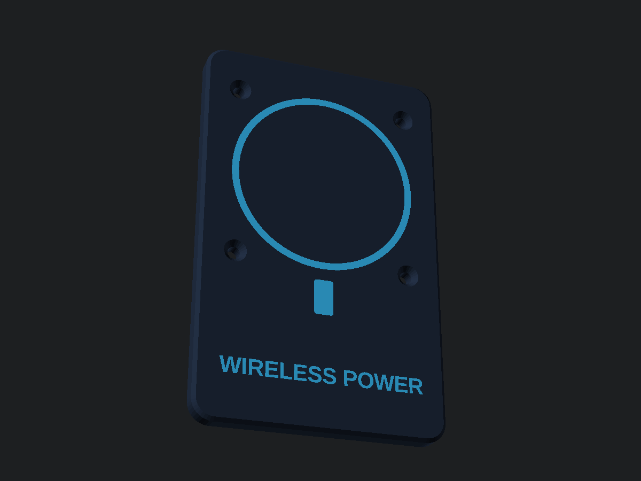
scad/vesa_wpt_multicolor.png
