Schepie/7segment/scad/vesa_wpt_puck_interior.png

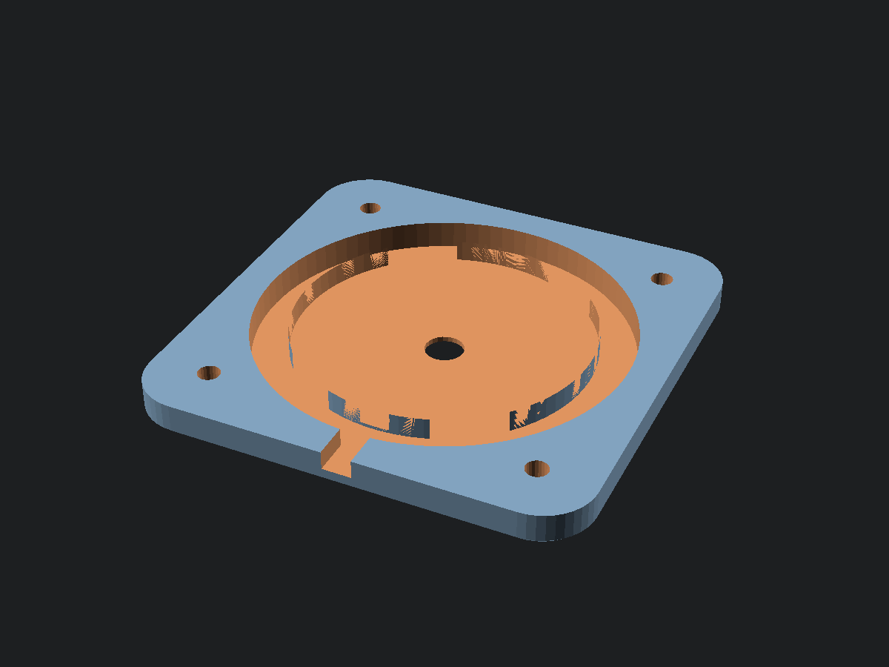
scad/vesa_wpt_puck_interior.png
