Schepie/7segment/scad/vesa_wpt_puck_rear.png

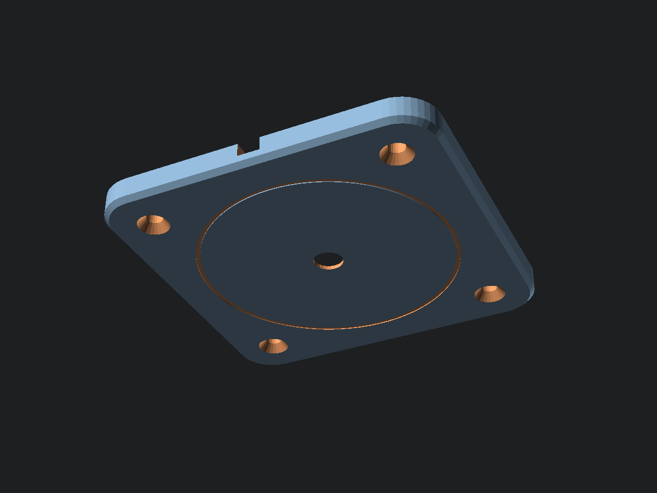
scad/vesa_wpt_puck_rear.png
