Schepie/7segment/scad/xyly01_bracelet_housing_both.png

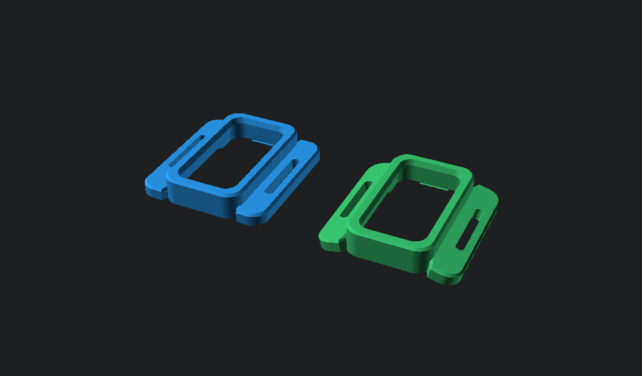
scad/xyly01_bracelet_housing_both.png
