Schepie/7segment/scad/xyly01_bracelet_housing_bottom.png

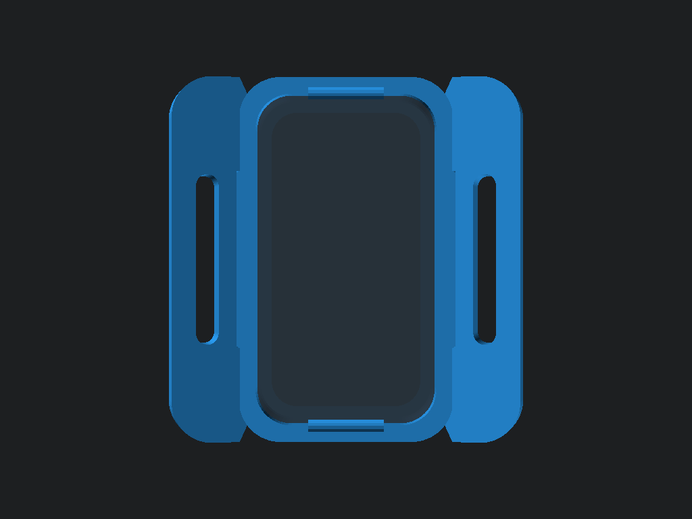
scad/xyly01_bracelet_housing_bottom.png
