Schepie/7segment/scad/xyly01_bracelet_housing_circular_closeup.png

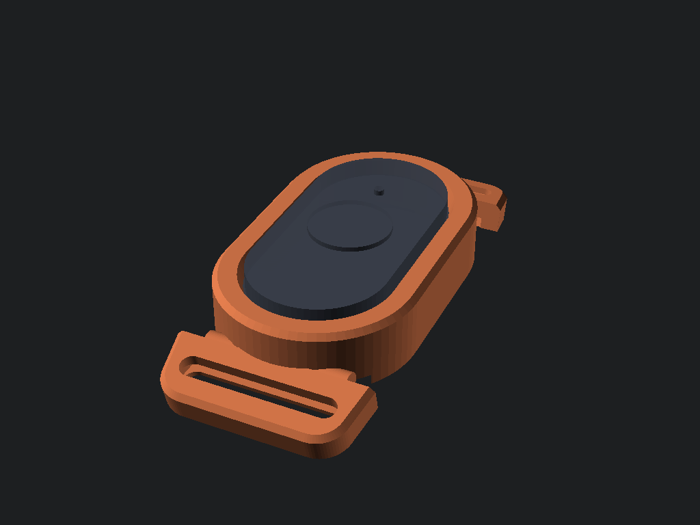
scad/xyly01_bracelet_housing_circular_closeup.png
