Schepie/7segment/scad/xyly01_bracelet_housing_cutaway.png

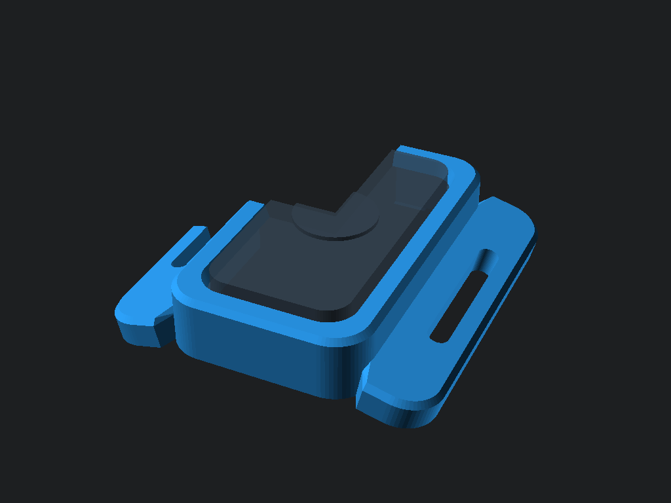
scad/xyly01_bracelet_housing_cutaway.png
