Schepie/7segment/scad/xyly01_bracelet_housing_preview.png

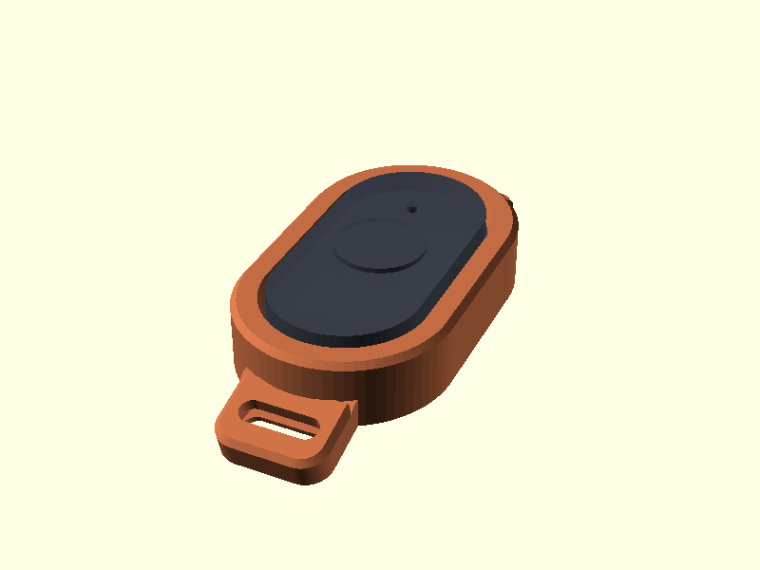
scad/xyly01_bracelet_housing_preview.png
