Schepie/7segment/scratch_board_crop.jpg

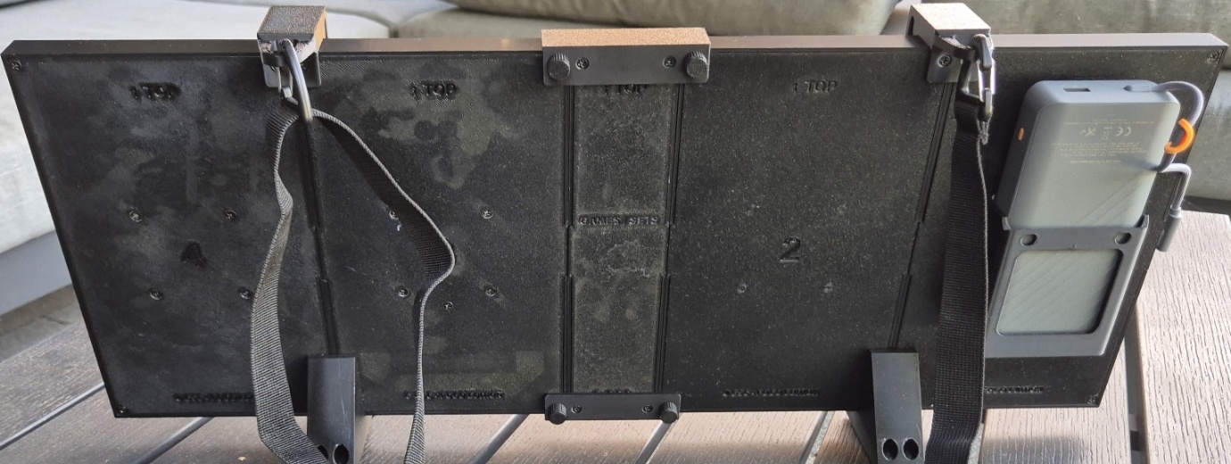
scratch_board_crop.jpg
