Schepie/7segment/scratch_board_masked.png

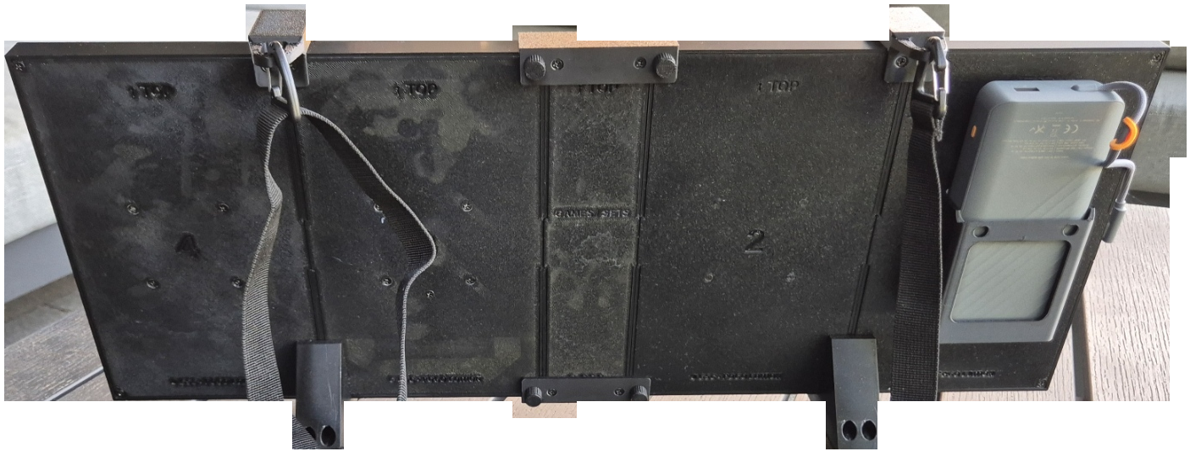
scratch_board_masked.png
