Schepie/7segment/scratch_court_bg.jpg

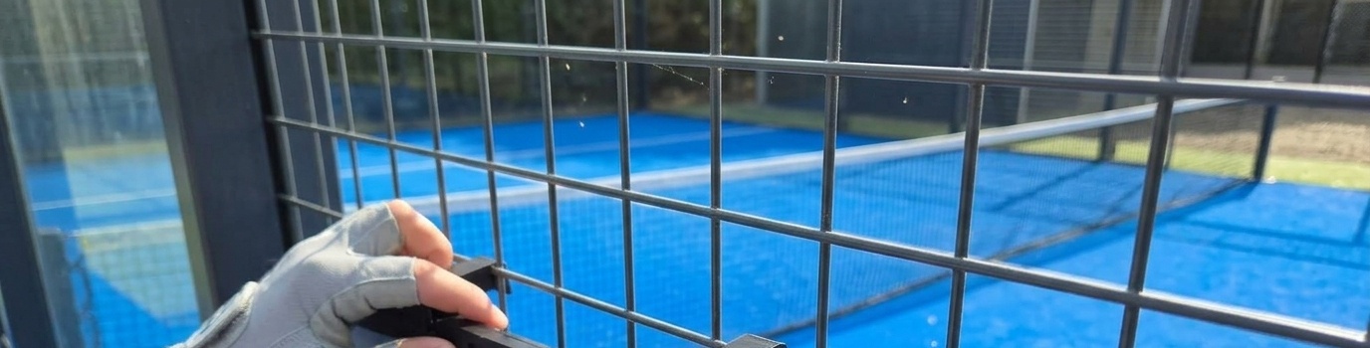
scratch_court_bg.jpg
