Schepie/7segment/scratch_crop_board_hd.png

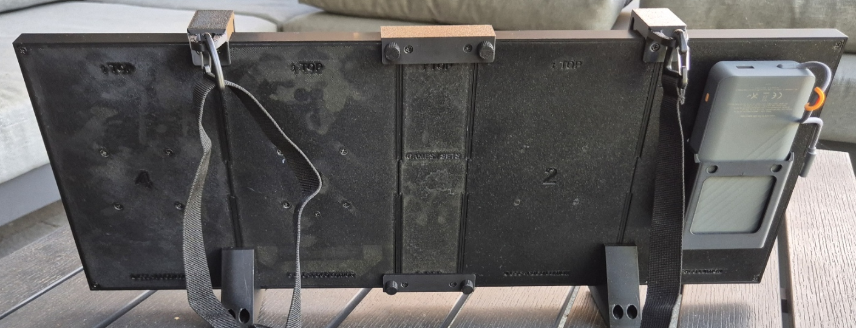
scratch_crop_board_hd.png
