Schepie/7segment/scratch_crop_hands.jpg

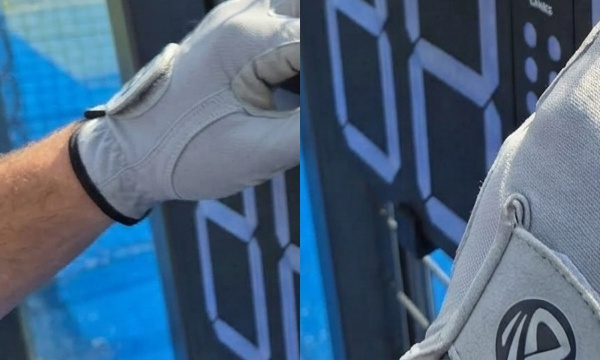
scratch_crop_hands.jpg
