Schepie/7segment/scratch_glove_mask.png

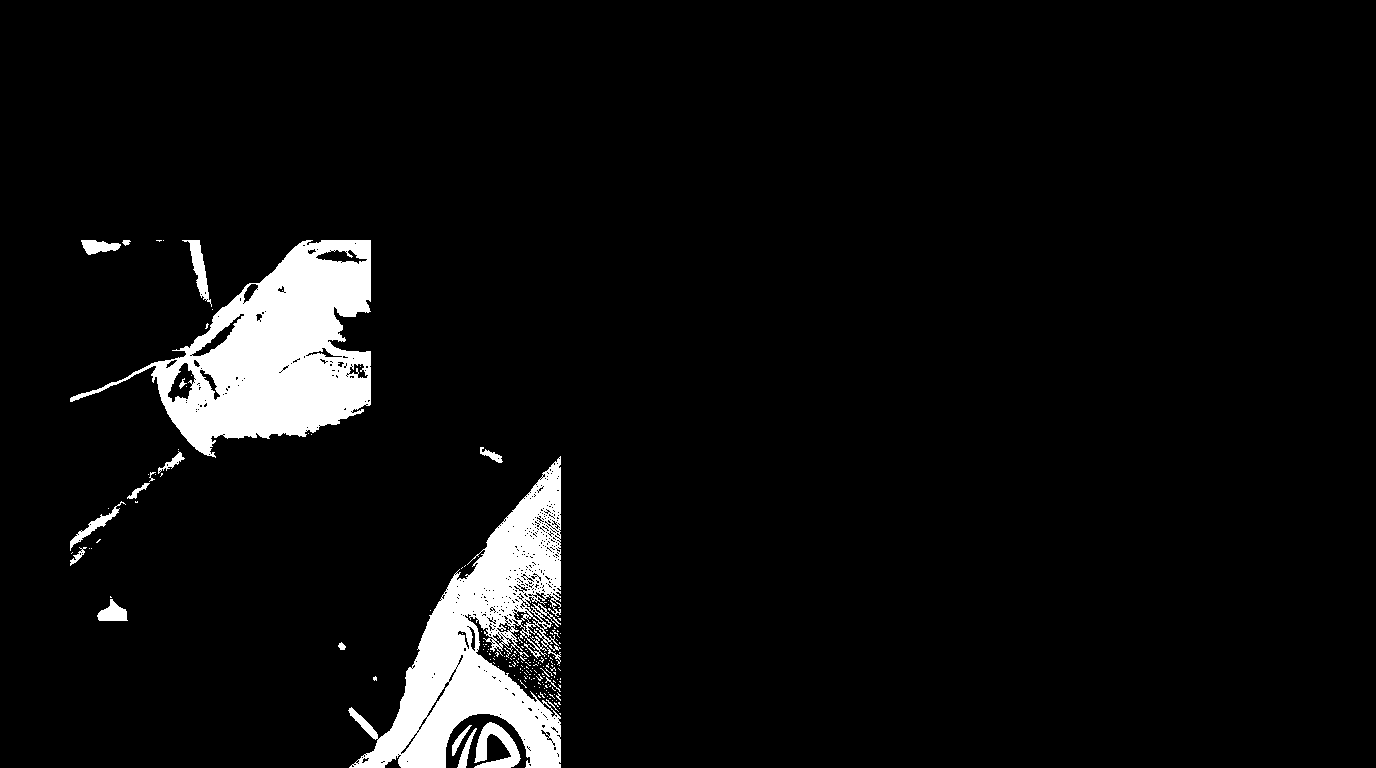
scratch_glove_mask.png
