Schepie/7segment/scratch_hand_l.jpg

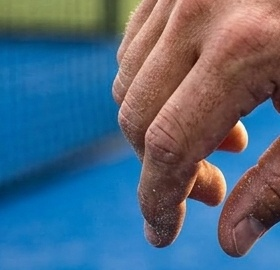
scratch_hand_l.jpg
