Schepie/7segment/scratch_hand_r.jpg

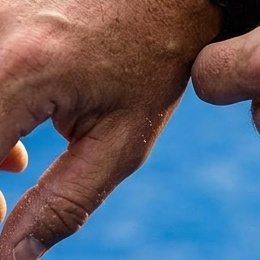
scratch_hand_r.jpg
