Schepie/7segment/scratch_rear_hanging_preview.jpg

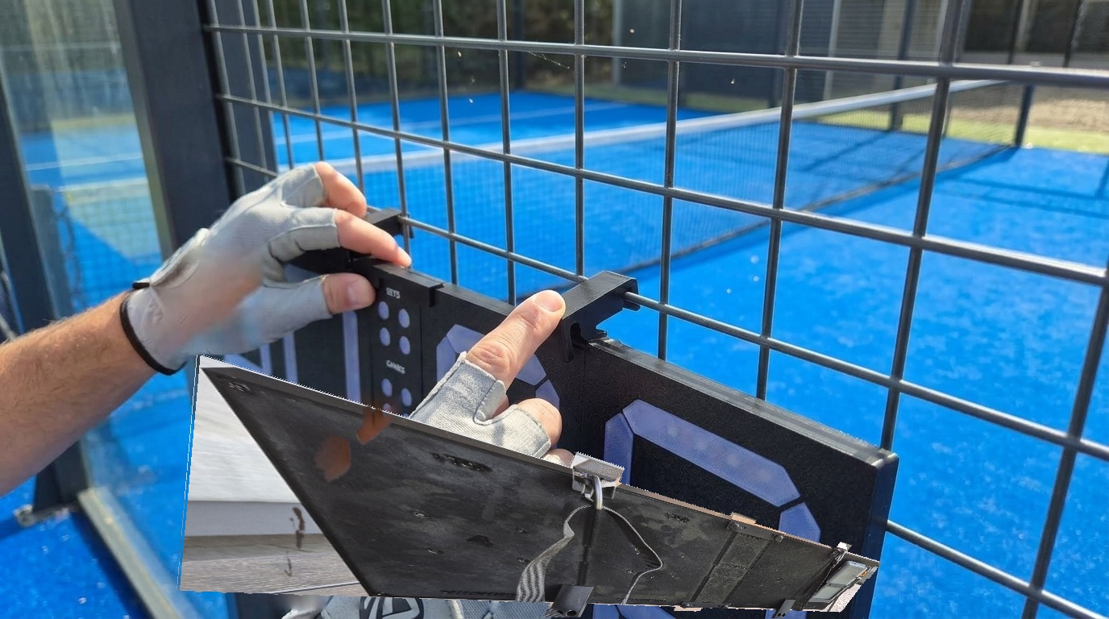
scratch_rear_hanging_preview.jpg
