Schepie/7segment/scad/panel3_backplate_wpt.stl

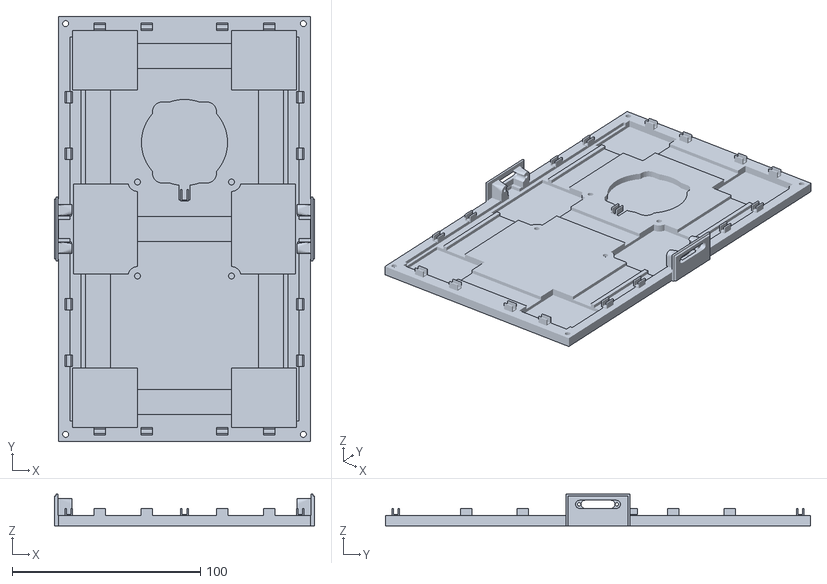
[picture p124: CAD file, 2026-09-22]
scad/panel3_backplate_wpt.stl
138.4 x 226.0 x 17.0
