Schepie/7segment/3d_models/display_stand_40mm.stl

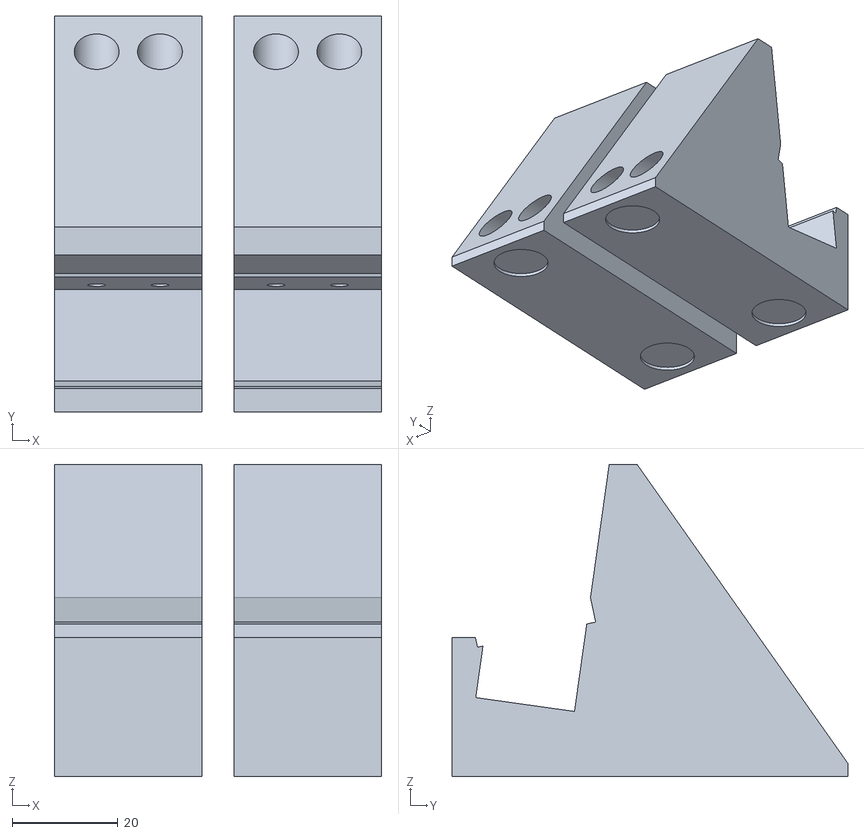
[picture p125: CAD file, 2026-09-16]
3d_models/display_stand_40mm.stl
62.0 x 75.1 x 59.2
