Schepie/7segment/scad/vesa_wpt_inlay.stl

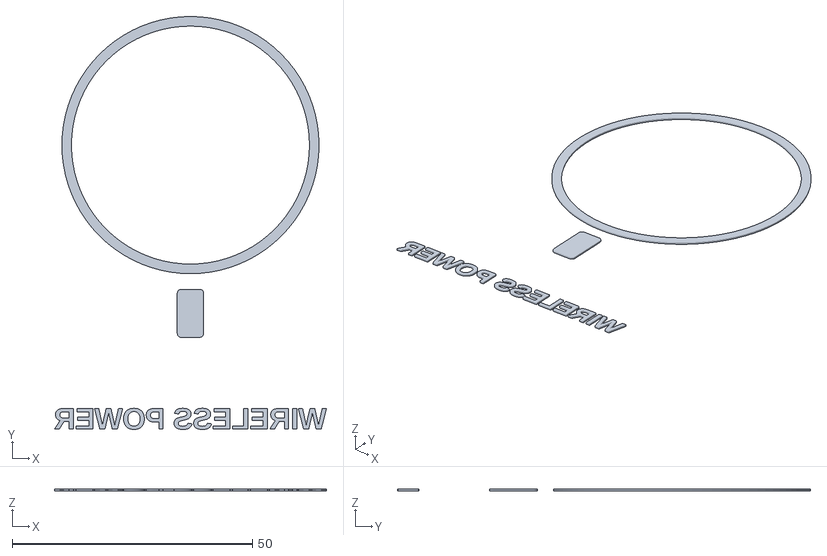
[picture p126: CAD file, 2026-09-22]
scad/vesa_wpt_inlay.stl
56.6 x 85.9 x 0.4
