Schepie/7segment/3d_models/games_sets_u_bracket.stl

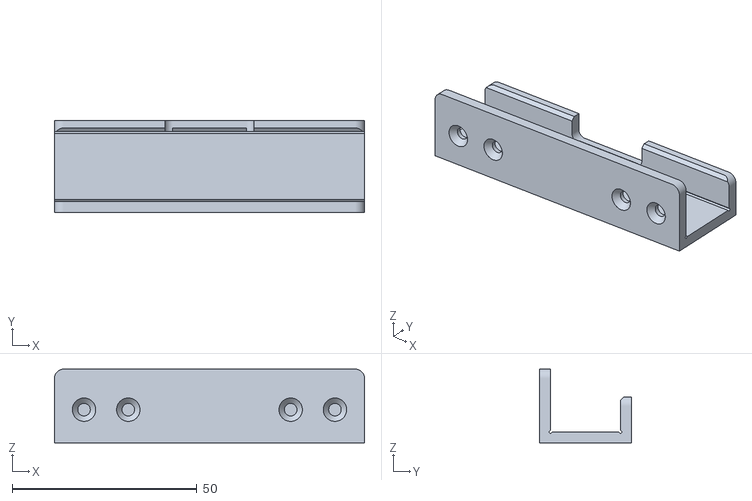
[picture p127: CAD file, 2026-09-16]
3d_models/games_sets_u_bracket.stl
84.0 x 24.9 x 20.0
