Schepie/7segment/scad/vesa_wpt_puck.stl

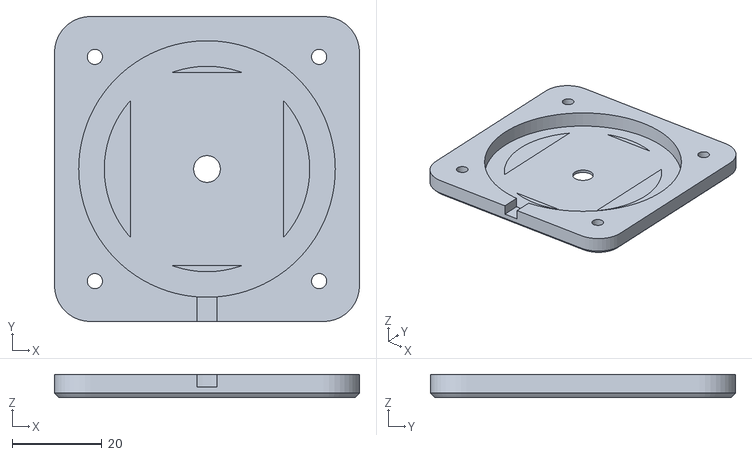
[picture p128: CAD file, 2026-09-22]
scad/vesa_wpt_puck.stl
68.0 x 68.0 x 5.20
