Schepie/7segment/3d_models/display_stand_cradle_single.stl

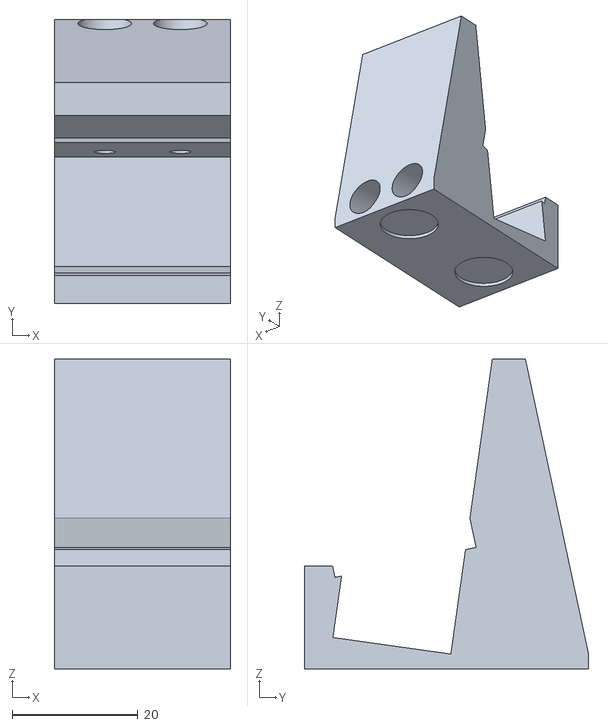
[picture p129: CAD file, 2026-09-16]
3d_models/display_stand_cradle_single.stl
28.0 x 45.1 x 49.2
