Schepie/7segment/3d_models/panel_seam_u_bracket.stl

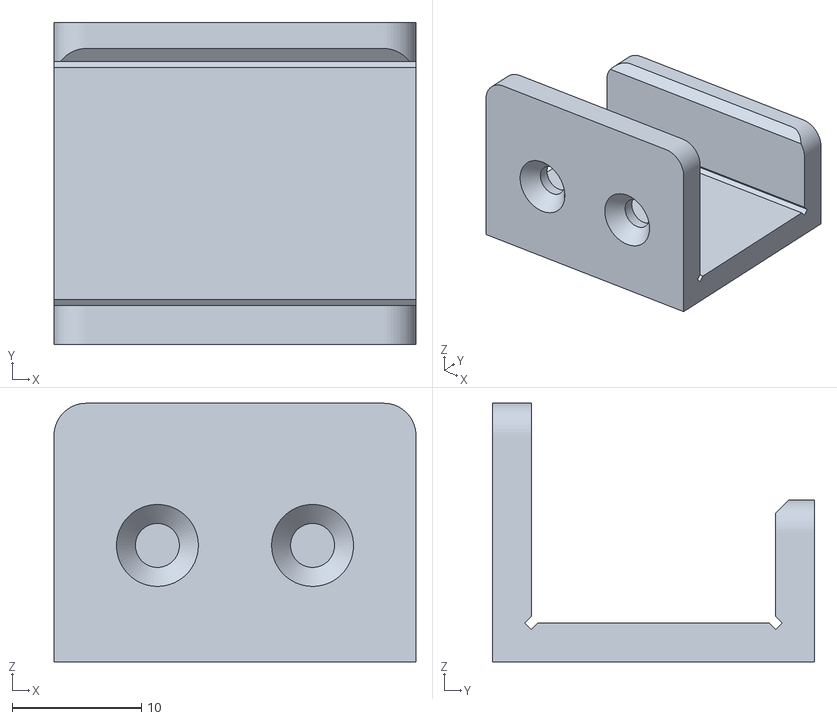
[picture p130: CAD file, 2026-09-16]
3d_models/panel_seam_u_bracket.stl
28.0 x 24.9 x 20.0
