Schepie/7segment/3d_models/games_sets_u_bracket_pair.stl

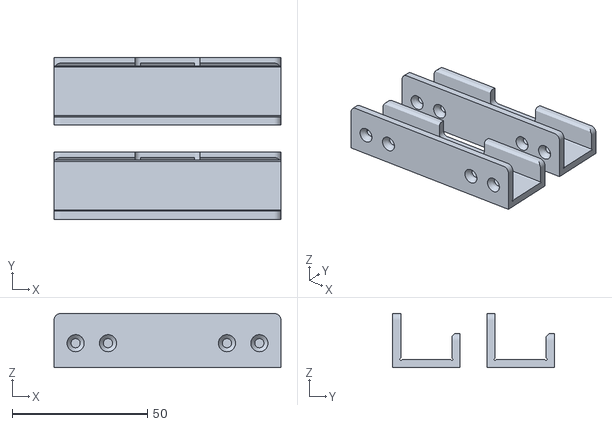
[picture p131: CAD file, 2026-09-16]
3d_models/games_sets_u_bracket_pair.stl
84.0 x 59.8 x 20.0
