Schepie/7segment/scad/xyly01_bracelet_housing_flat.stl

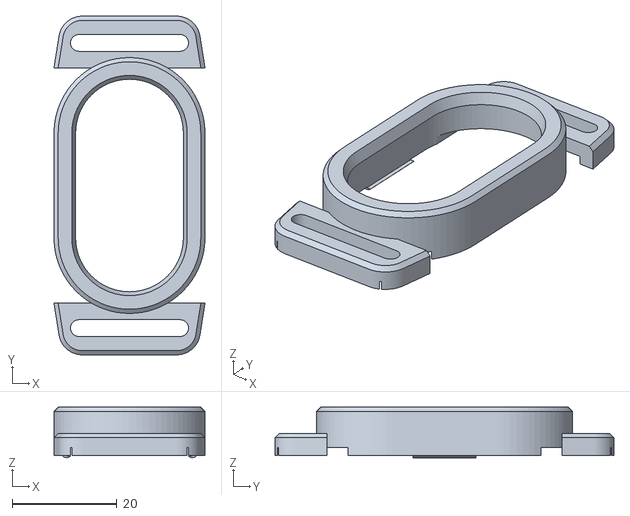
[picture p132: CAD file, 2026-09-22]
scad/xyly01_bracelet_housing_flat.stl
28.8 x 64.6 x 9.65
