Schepie/7segment/3d_models/display_stand.stl

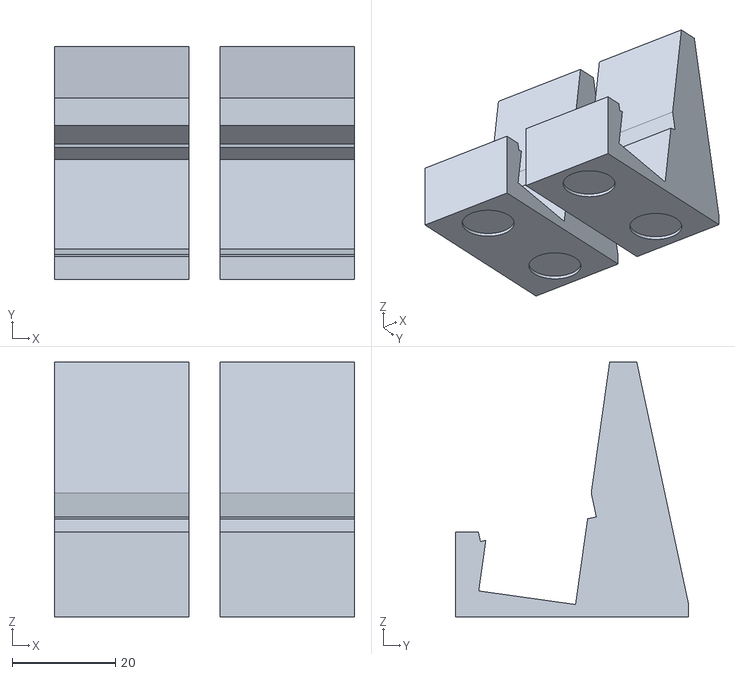
[picture p133: CAD file, 2026-09-15]
3d_models/display_stand.stl
58.0 x 45.1 x 49.2
