Schepie/7segment/scad/xyly01_bracelet_housing2.stl

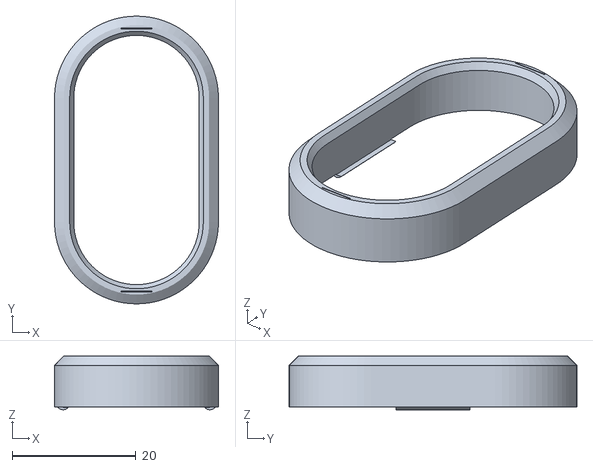
[picture p134: CAD file, 2026-09-22]
scad/xyly01_bracelet_housing2.stl
26.5 x 46.5 x 8.70
