Schepie/7segment/3d_models/padel_hook.stl

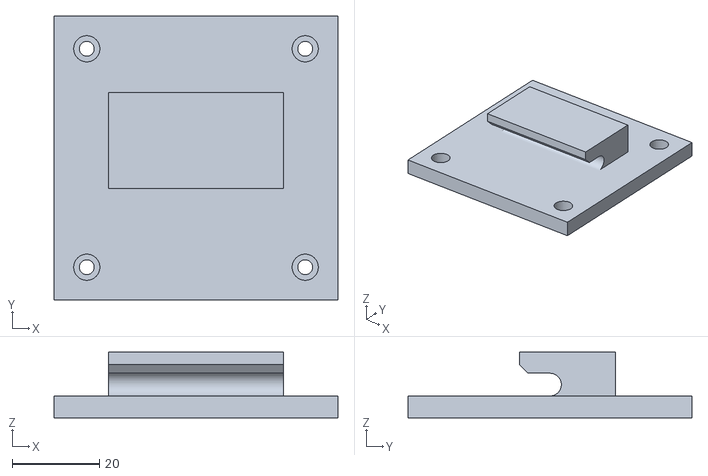
[picture p135: CAD file, 2026-09-07]
3d_models/padel_hook.stl
65.0 x 65.0 x 15.0
