Schepie/7segment/scad/xyly01_bracelet_housing.stl

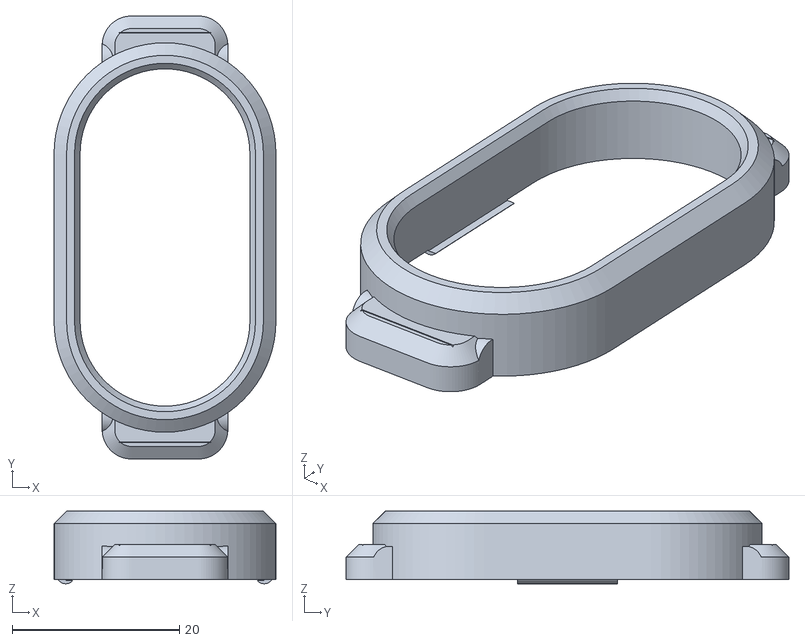
[picture p136: CAD file, 2026-09-22]
scad/xyly01_bracelet_housing.stl
26.5 x 52.9 x 8.70
