Schepie/7segment/3d_models/remote_strap_holder.stl

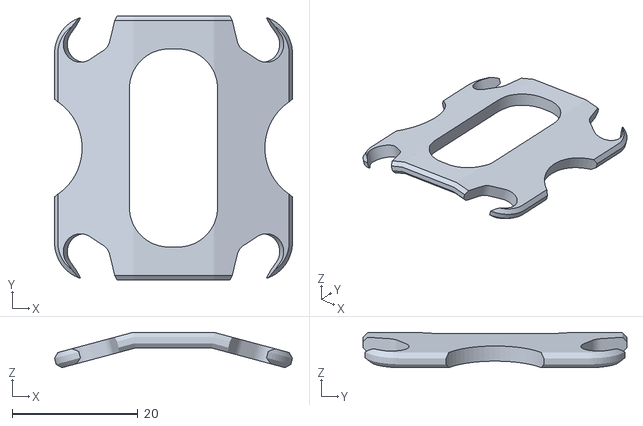
[picture p137: CAD file, 2026-09-06]
3d_models/remote_strap_holder.stl
37.9 x 42.0 x 5.63
