Schepie/7segment/scad/remote_strap_holder_flat.stl

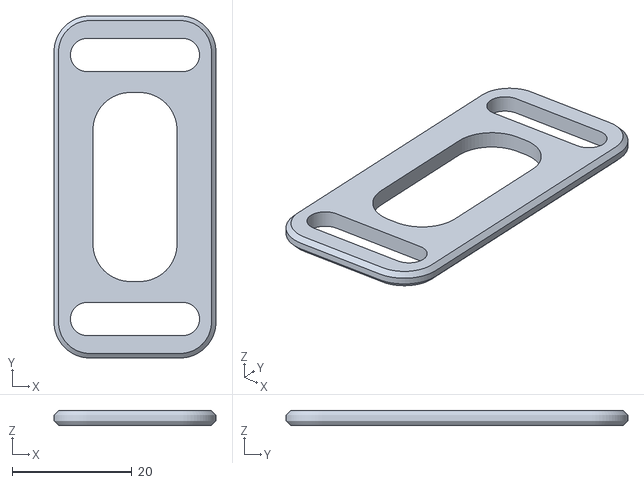
[picture p138: CAD file, 2026-09-20]
scad/remote_strap_holder_flat.stl
27.0 x 57.0 x 2.50
