Schepie/7segment/3d_models/digit_set_7segments_white.stl

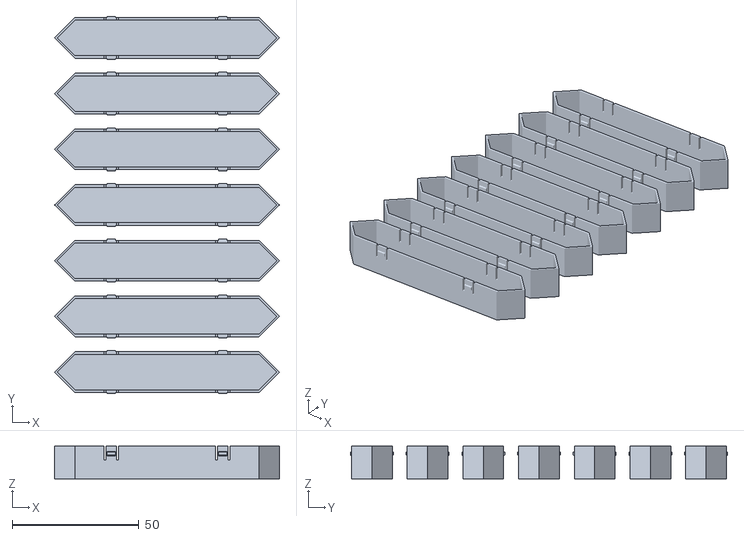
[picture p139: CAD file, 2026-09-06]
3d_models/digit_set_7segments_white.stl
88.9 x 149.0 x 13.0
