Schepie/7segment/3d_models/games_sets_pogo_snap_individual_dots.stl

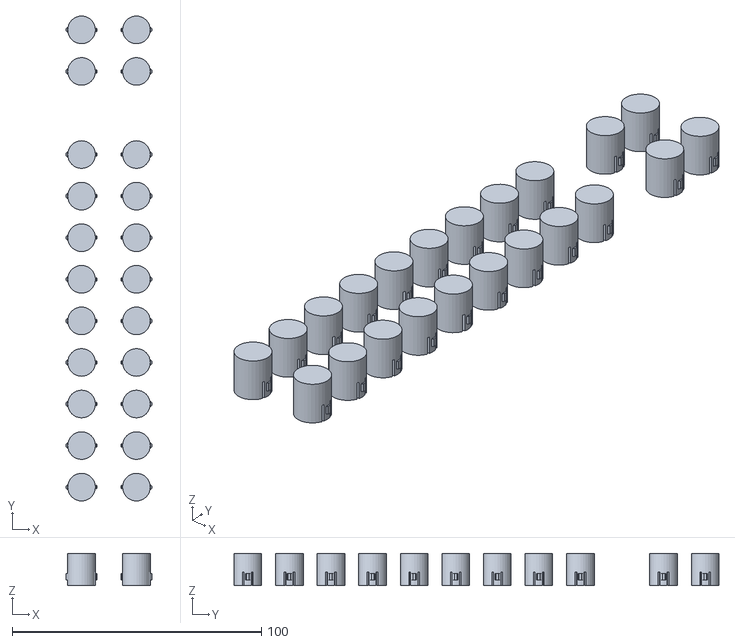
[picture p140: CAD file, 2026-09-06]
3d_models/games_sets_pogo_snap_individual_dots.stl
34.4 x 194.4 x 13.0
