Schepie/7segment/scad/panel_seam_u_bracket_set4.stl

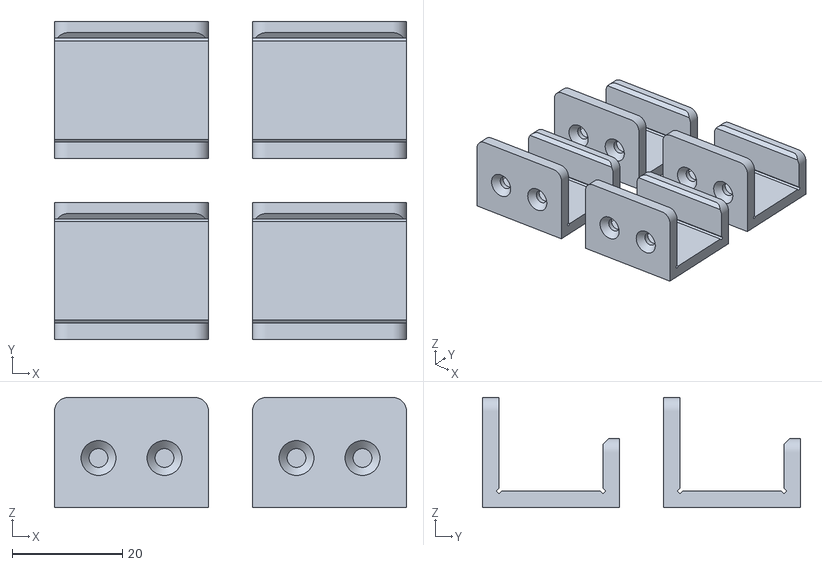
[picture p141: CAD file, 2026-09-16]
scad/panel_seam_u_bracket_set4.stl
64.0 x 57.8 x 20.0
