Schepie/7segment/3d_models/7segment_pogo_FP_4.stl

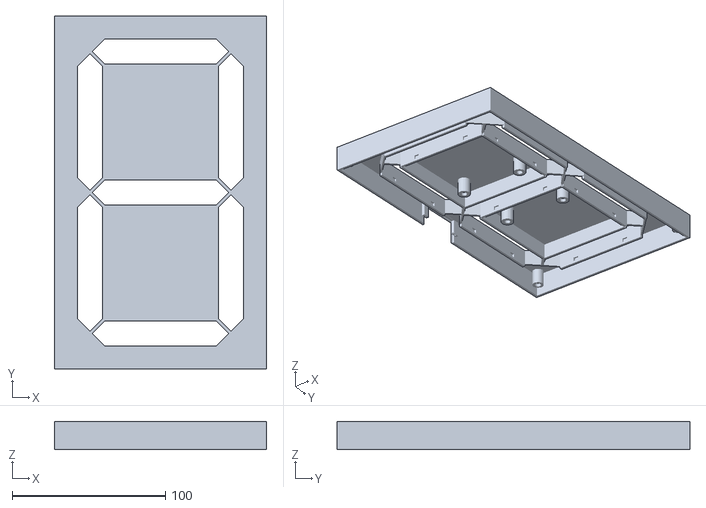
[picture p142: CAD file, 2026-09-06]
3d_models/7segment_pogo_FP_4.stl
138.4 x 230.4 x 18.5
