Schepie/7segment/scad/panel_seam_u_hook_bracket.stl

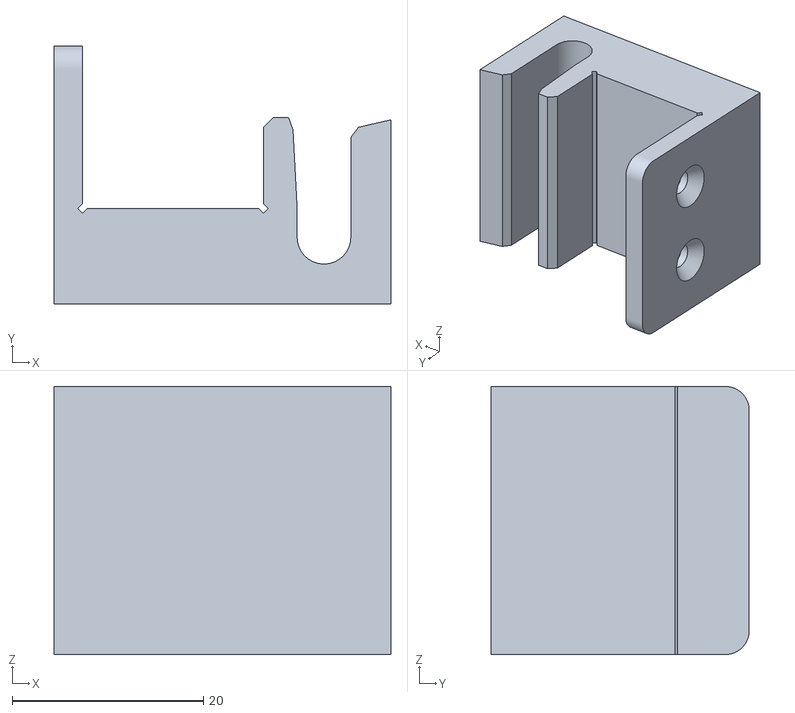
[picture p143: CAD file, 2026-09-16]
scad/panel_seam_u_hook_bracket.stl
35.2 x 27.0 x 28.0
