Schepie/7segment/3d_models/single_segment_white.stl

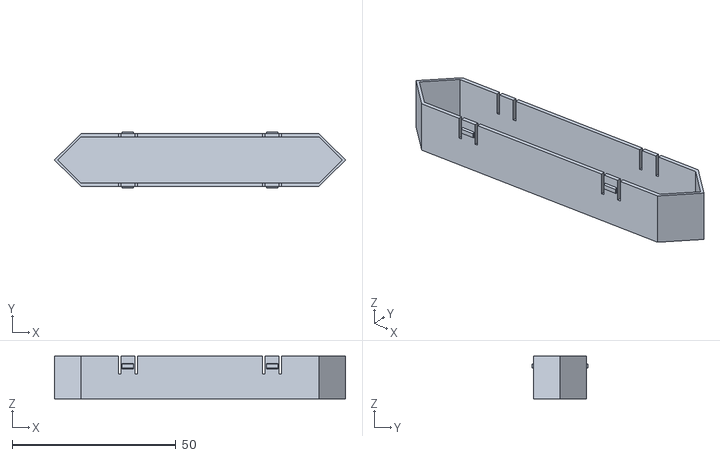
[picture p145: CAD file, 2026-09-06]
3d_models/single_segment_white.stl
88.9 x 17.0 x 13.0
