Schepie/7segment/3d_models/remote_strap_holder_flat.stl

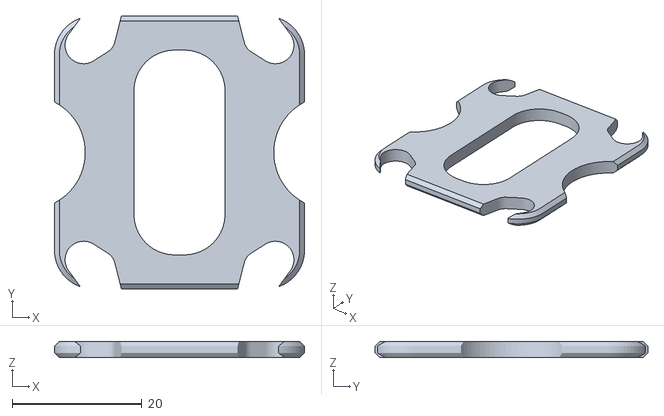
[picture p146: CAD file, 2026-09-06]
3d_models/remote_strap_holder_flat.stl
38.5 x 42.0 x 2.50
