Schepie/7segment/3d_models/games_sets_pogo_snap_individual_dots_FPB.stl

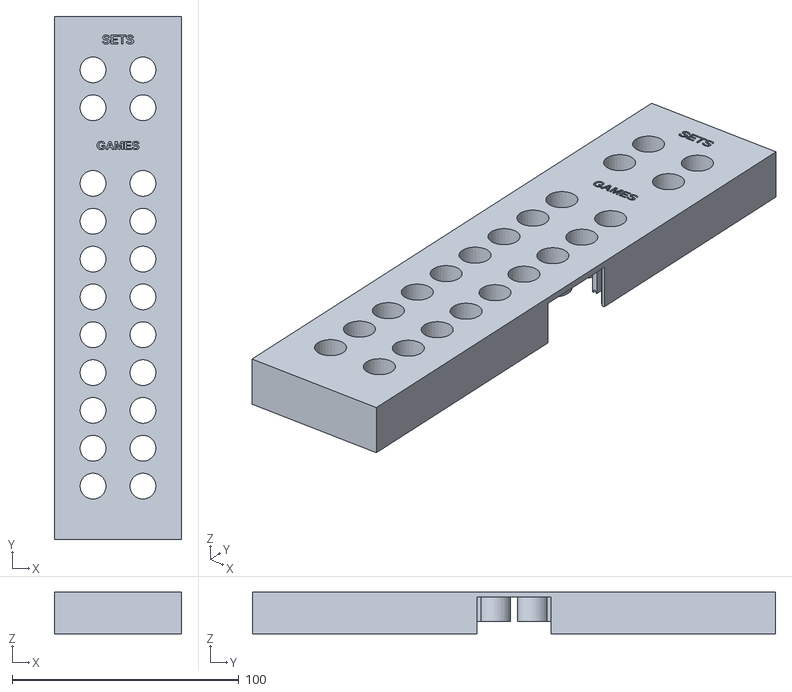
[picture p147: CAD file, 2026-09-06]
3d_models/games_sets_pogo_snap_individual_dots_FPB.stl
56.0 x 230.4 x 18.5
