Schepie/7segment/3d_models/7segment_pogo back4.stl

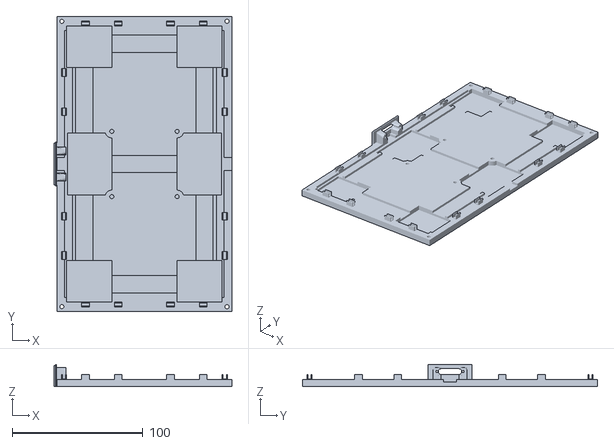
[picture p148: CAD file, 2026-09-06]
3d_models/7segment_pogo back4.stl
136.2 x 226.0 x 17.0
