Schepie/7segment/3d_models/rear_corner_foot_set4.stl

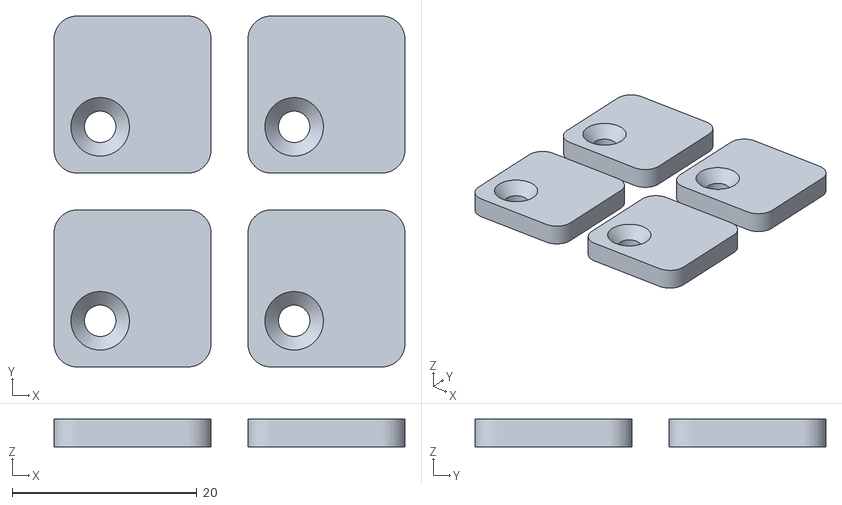
[picture p149: CAD file, 2026-09-06]
3d_models/rear_corner_foot_set4.stl
38.0 x 38.0 x 3.00
