Schepie/7segment/3d_models/7segment_pogo back2.stl

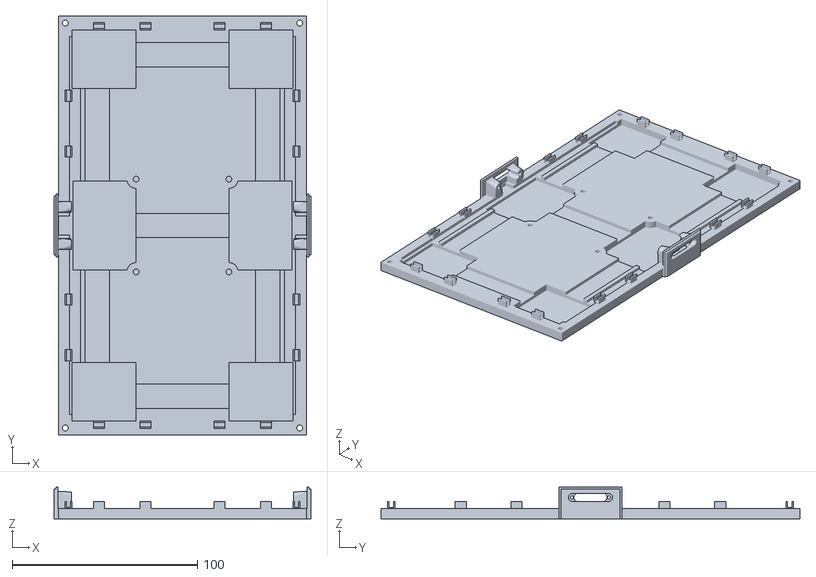
[picture p150: CAD file, 2026-09-06]
3d_models/7segment_pogo back2.stl
138.4 x 226.0 x 17.0
