Schepie/7segment/3d_models/games_sets_pogo_snap_individual_dots_txt.stl

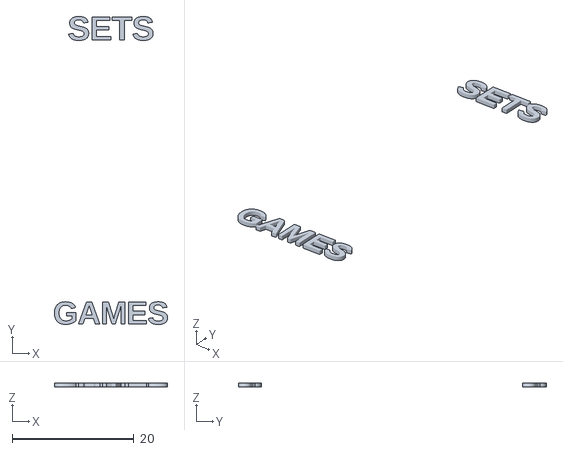
[picture p151: CAD file, 2026-09-06]
3d_models/games_sets_pogo_snap_individual_dots_txt.stl
18.6 x 50.5 x 0.6
