Schepie/7segment/3d_models/rear_joining_bracket_hinged.stl

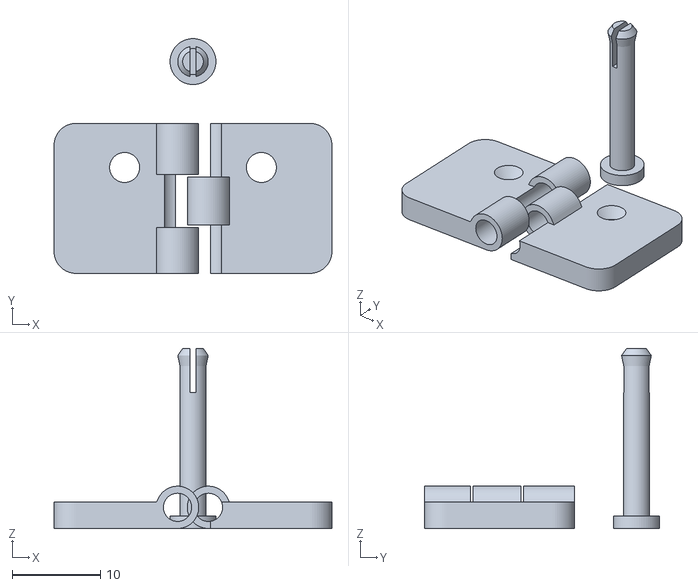
[picture p152: CAD file, 2026-09-06]
3d_models/rear_joining_bracket_hinged.stl
31.5 x 26.6 x 20.4
