Schepie/7segment/scad/panel_insert_stud_pair.stl

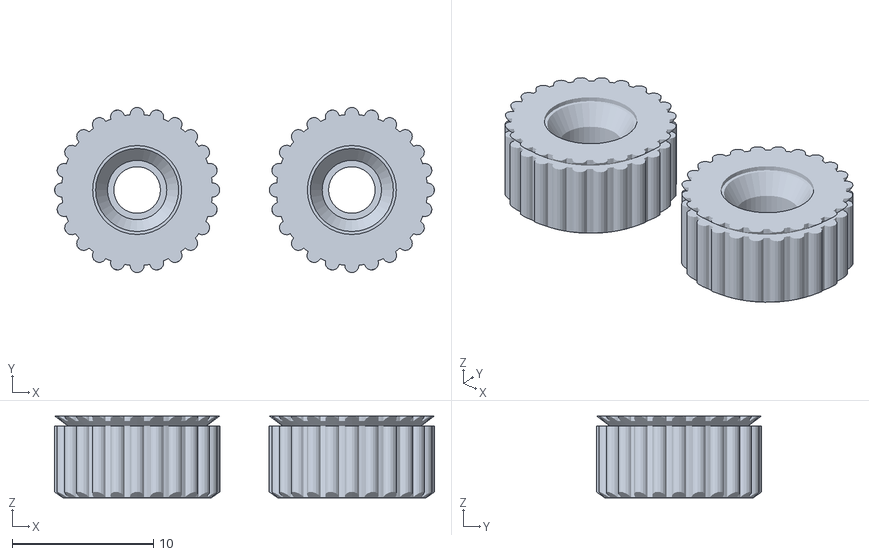
[picture p153: CAD file, 2026-09-15]
scad/panel_insert_stud_pair.stl
26.9 x 11.7 x 5.80
