Schepie/7segment/3d_models/games_sets_pogo_snap_individual_dots_back.stl

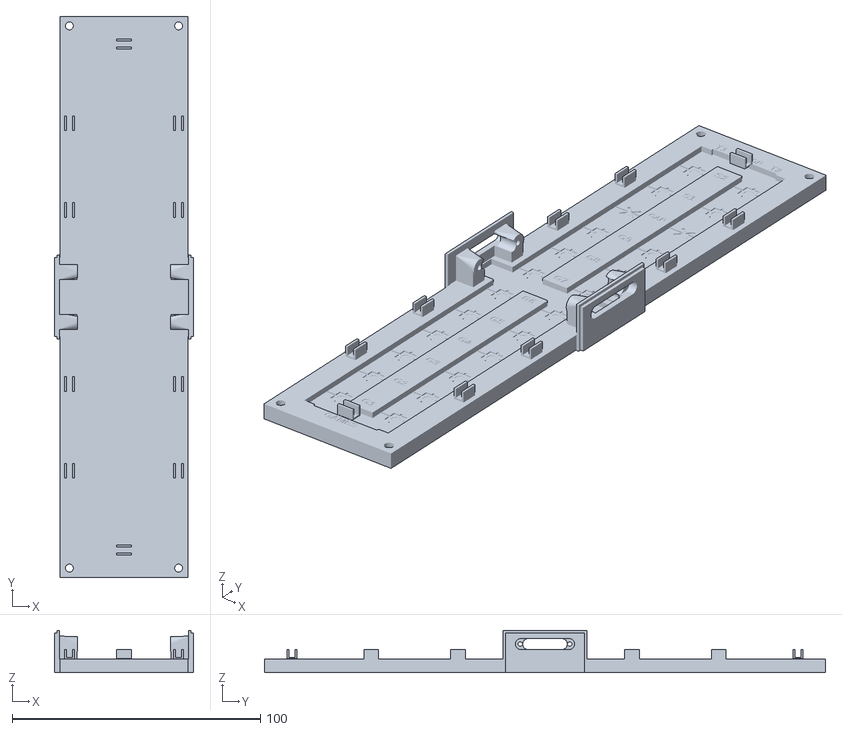
[picture p154: CAD file, 2026-09-06]
3d_models/games_sets_pogo_snap_individual_dots_back.stl
56.0 x 226.0 x 17.0
