Schepie/7segment/3d_models/rear_joining_bracket.stl

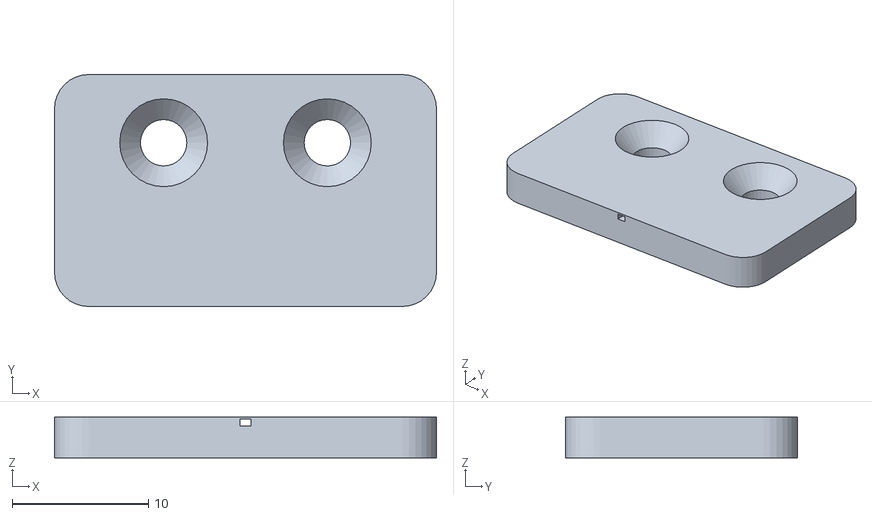
[picture p155: CAD file, 2026-09-06]
3d_models/rear_joining_bracket.stl
28.0 x 17.0 x 3.00
