Schepie/7segment/3d_models/rear_corner_foot.stl

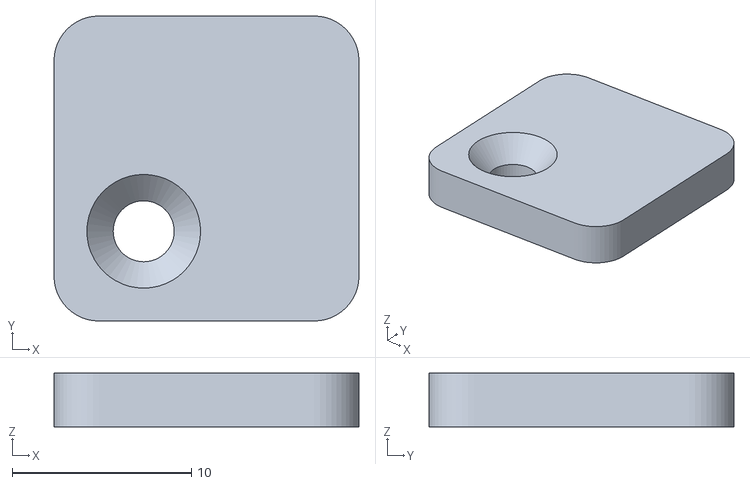
[picture p156: CAD file, 2026-09-06]
3d_models/rear_corner_foot.stl
17.0 x 17.0 x 3.00
