Schepie/7segment/scad/display_stand_cradle_single.stl

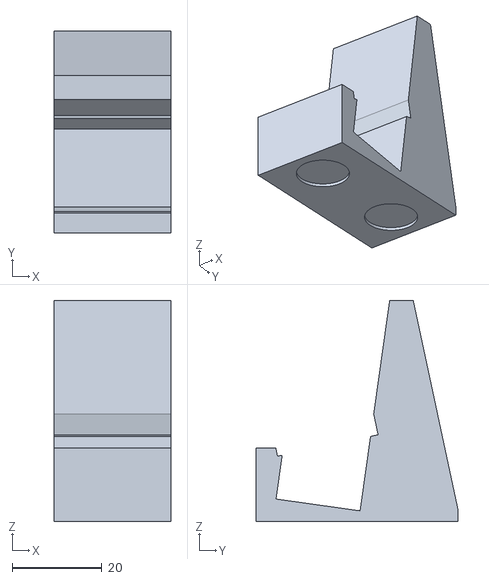
[picture p157: CAD file, 2026-09-15]
scad/display_stand_cradle_single.stl
26.0 x 45.1 x 49.2
