Schepie/7segment/scad/rear_corner_foot_pair.stl

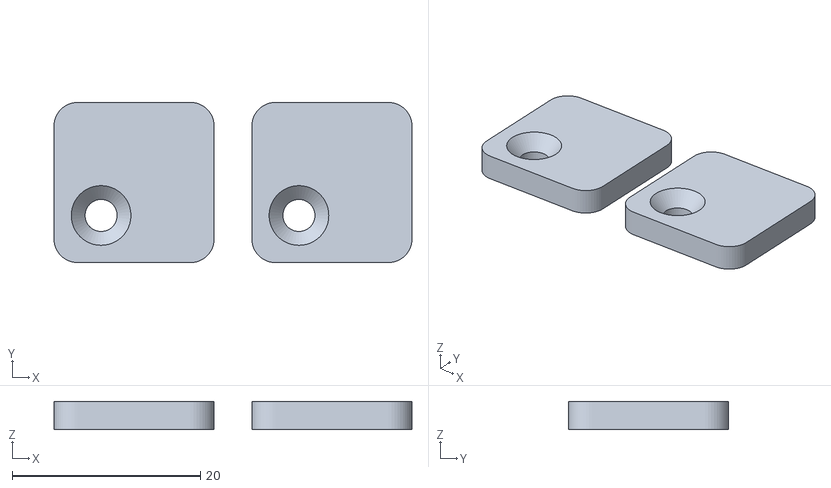
[picture p158: CAD file, 2026-09-06]
scad/rear_corner_foot_pair.stl
38.0 x 17.0 x 3.00
