Schepie/7segment/scad/single_segment_white_nosnaps.stl

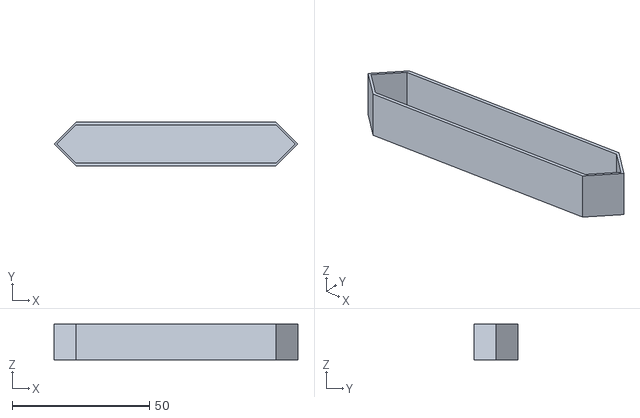
[picture p159: CAD file, 2026-09-06]
scad/single_segment_white_nosnaps.stl
88.9 x 16.1 x 13.0
