Schepie/7segment/scad/rear_joining_bracket_hinged_pin.stl

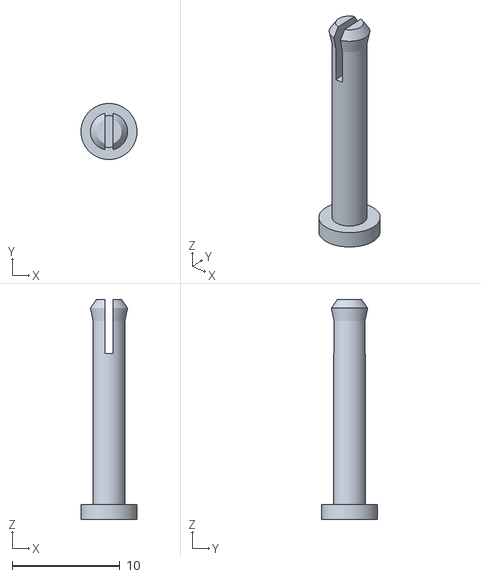
[picture p160: CAD file, 2026-09-06]
scad/rear_joining_bracket_hinged_pin.stl
5.20 x 5.20 x 20.4
