Schepie/7segment/scad/rear_joining_bracket_hinged_right.stl

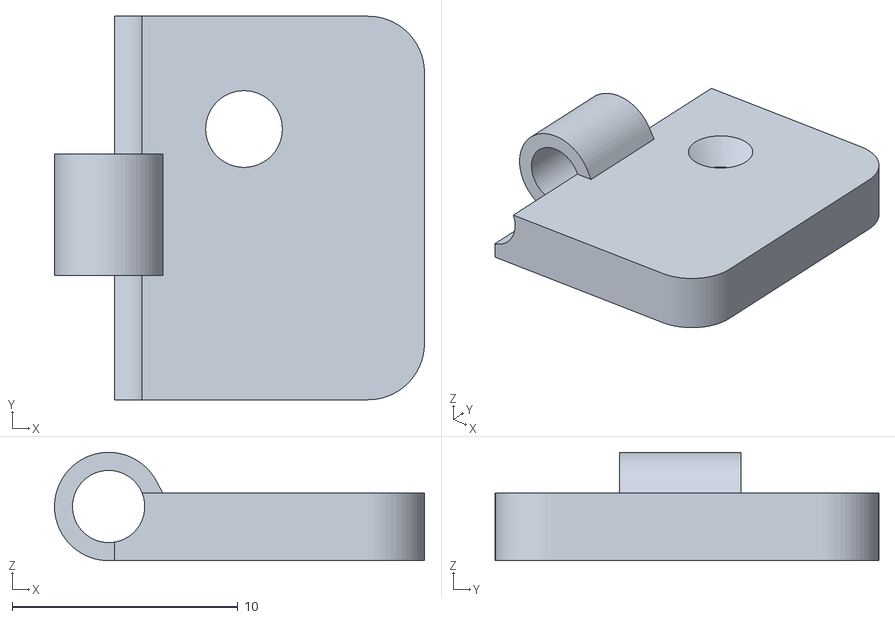
[picture p161: CAD file, 2026-09-06]
scad/rear_joining_bracket_hinged_right.stl
16.4 x 17.0 x 4.80
