Schepie/7segment/scad/7segment_pogo_back.stl

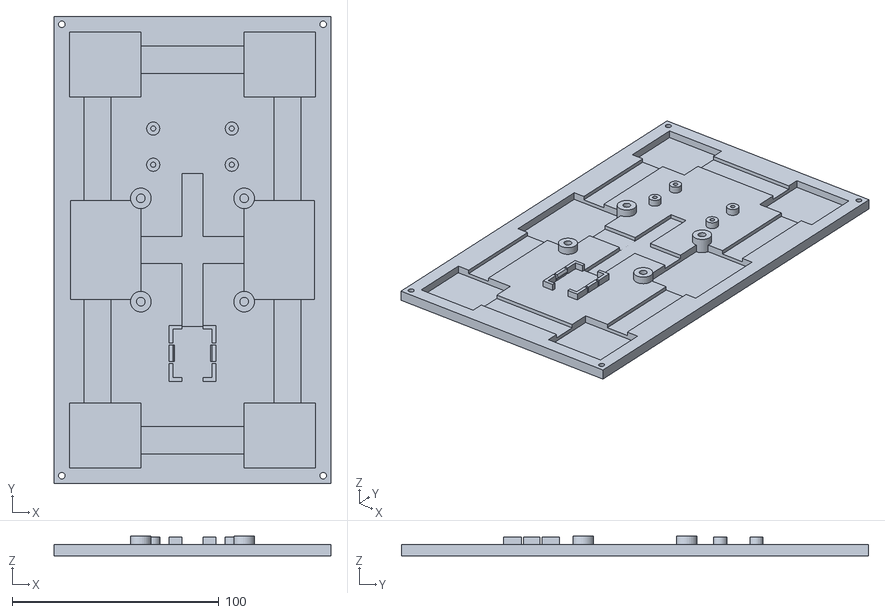
[picture p163: CAD file, 2026-09-01]
scad/7segment_pogo_back.stl
134.0 x 226.0 x 9.50
