Schepie/7segment/scad/7segment_pogo_front.stl

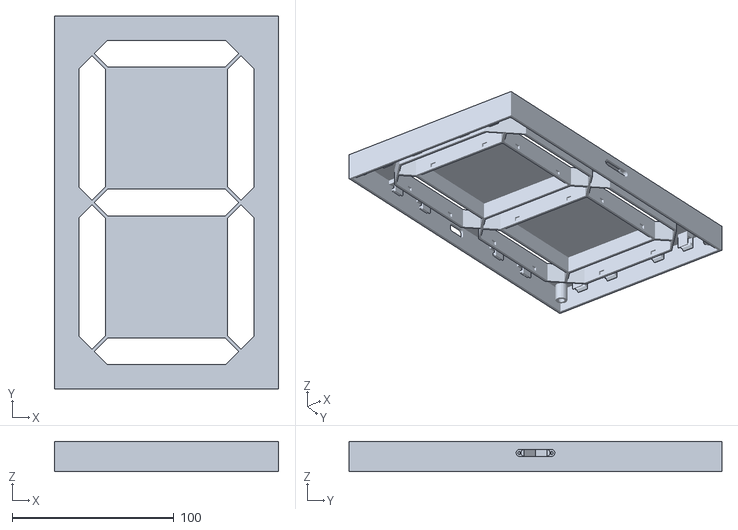
[picture p164: CAD file, 2026-09-01]
scad/7segment_pogo_front.stl
138.4 x 230.4 x 18.6
