Schepie/7segment/scad/7segment_lightguide_0.6mm.scad

// 7-Segment Lightguide / Diffuser - 0.6 mm Variant
// High brightness / maximum light transmission variant
include <7segment_lightguide.scad>
frontplate_white(d_thick = 0.6);
