Schepie/7segment/scad/7segment_lightguide_0.8mm.scad

// 7-Segment Lightguide / Diffuser - 0.8 mm Variant
// Balanced light diffusion and brightness variant
include <7segment_lightguide.scad>
frontplate_white(d_thick = 0.8);
