Schepie/7segment/scad/backplate_only.scad

use <7segment_v2.scad>

// Render just the backplate to see the new soldering pockets
color("SlateGray") backplate();
