Schepie/7segment/scad/frontplate_only.scad

use <7segment_v2.scad>

// Render just the black frontplate so the user can see the updated margins
color("DimGray") frontplate_black();
