Schepie/7segment/Images/display_stand_assembly_preview.png

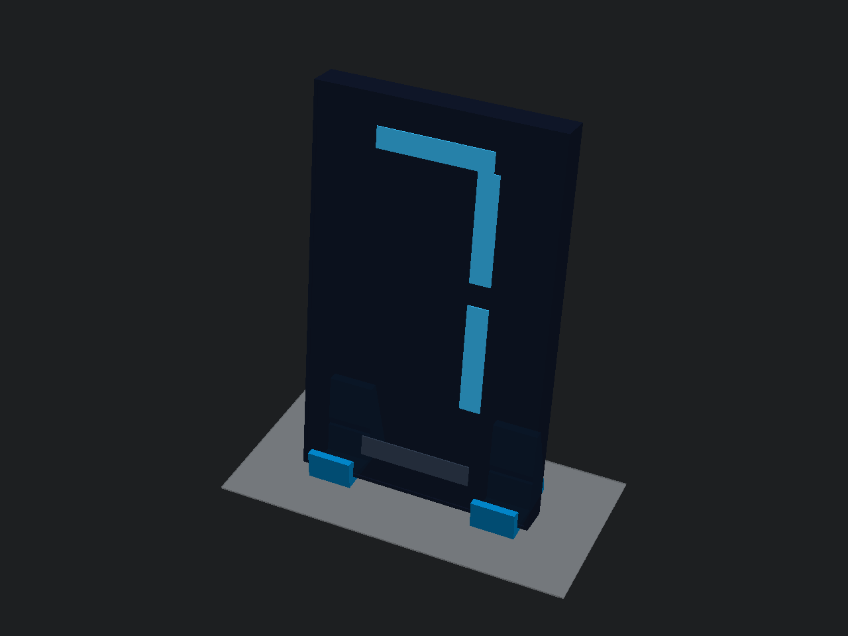
Images/display_stand_assembly_preview.png
