Schepie/7segment/scad/display_stand_seam_assembly.png

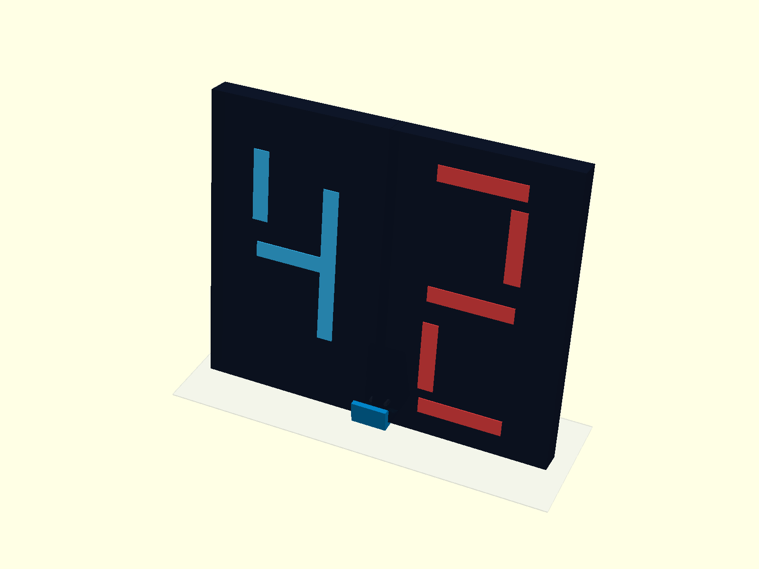
scad/display_stand_seam_assembly.png
