Schepie/7segment/scad/games_sets_sets_assembly_perspective.png

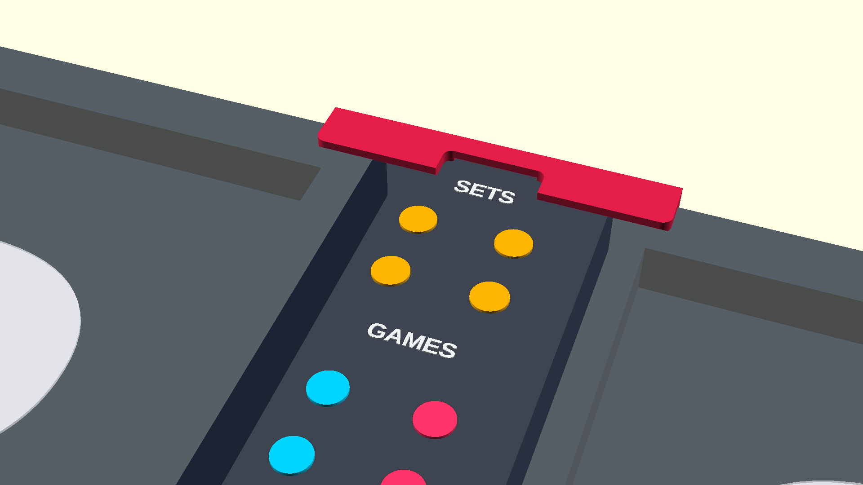
scad/games_sets_sets_assembly_perspective.png
