Schepie/7segment/scad/games_sets_u_bracket_assembly.png

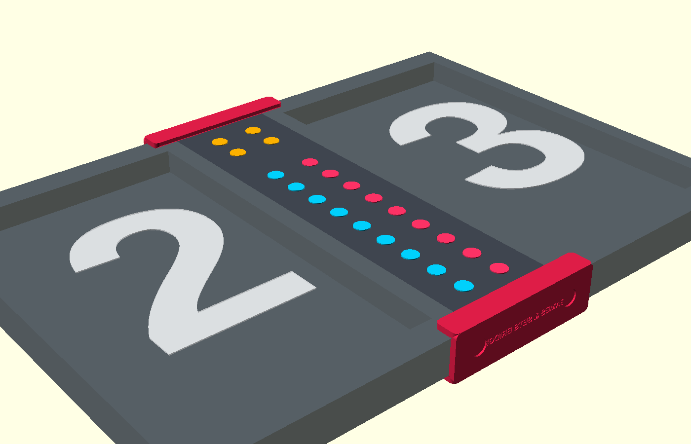
scad/games_sets_u_bracket_assembly.png
