Schepie/7segment/scad/games_sets_u_bracket_assembly_rear.png

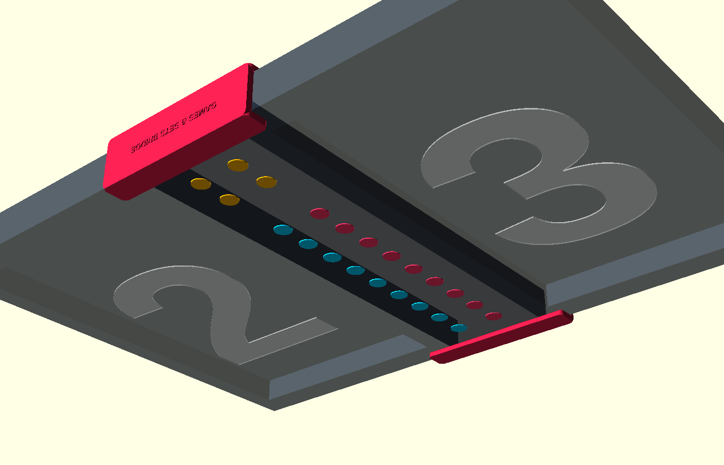
scad/games_sets_u_bracket_assembly_rear.png
