Schepie/7segment/scad/panel_seam_u_bracket_assembly_backplate.png

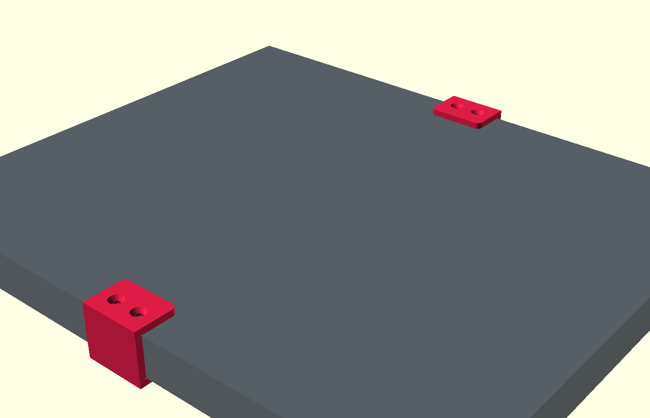
scad/panel_seam_u_bracket_assembly_backplate.png
