Schepie/7segment/scad/rear_joining_bracket_hinged_assembled.png

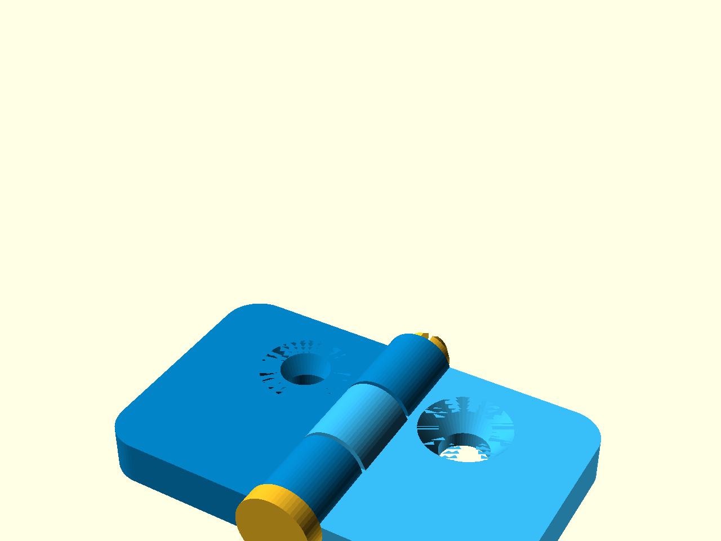
scad/rear_joining_bracket_hinged_assembled.png
