Schepie/7segment/scad/vesa_wpt_70x110_assembled.png

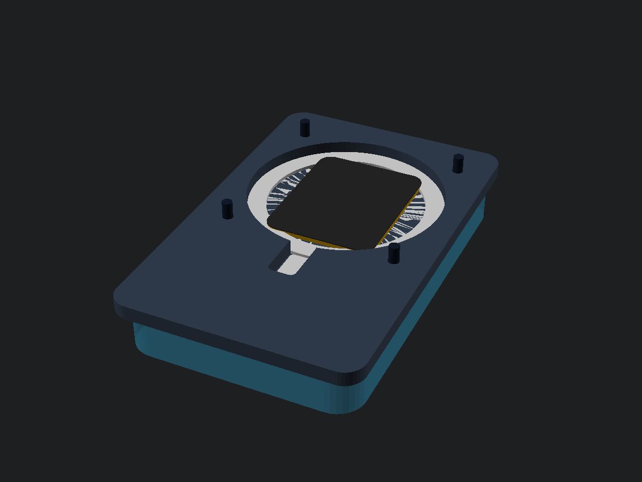
scad/vesa_wpt_70x110_assembled.png
