Schepie/7segment/scad/vesa_wpt_assembled.png

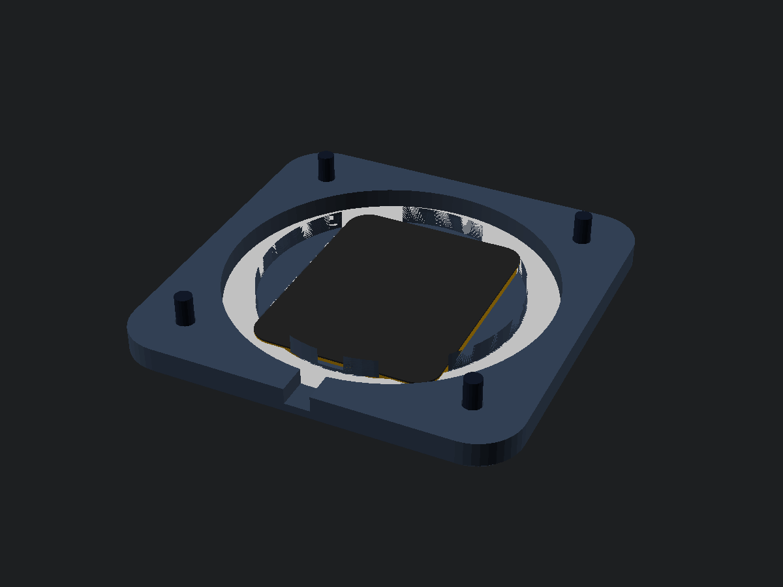
scad/vesa_wpt_assembled.png
