Schepie/7segment/scad/vesa_wpt_test_view.png

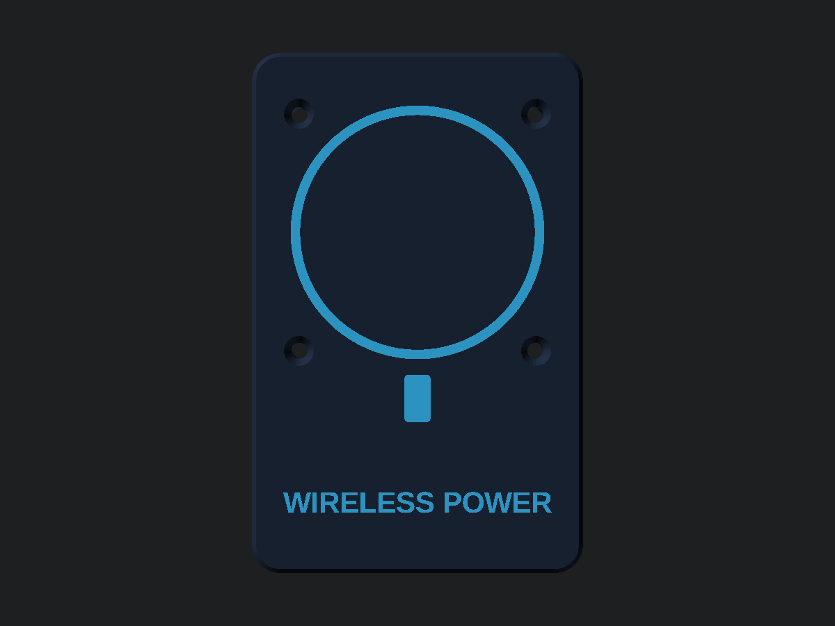
scad/vesa_wpt_test_view.png
